TPMJB/K-UI-NeXT/docs/evidence/launch-recovery-disc-stop-2026-10-06.md

# Launch recovery and optical idle

The checksum-batching test `8f7ea7925344` stopped tested games at the detached stage's `INVALID RETAIL MAP`, detail 1. The launch-preparation implementation is restored exactly to working `606f74248d5c` source. Existing GD command fixes, format support and the RAM game catalogue remain. This is a recovery candidate; console confirmation remains required. The precise cause of the failed native handoff is not established.

The boot/recovery menu and SD runtime draw their first screen, then submit firmware `CD_CMD_STOP` before creating the I/O worker. The command uses the existing bounded command adapter: three seconds, then one second for abort recovery. It refuses active DMA and a poisoned adapter. Cleanup ignores held B, and it submits no disc INIT, TOC or read command. Bus/syscall setup is separate from media initialization. The pinned KOS stop command is used directly because its convenience spin-down wrapper has no timeout.

Runtime idle title detection starts parked. Status polling cannot trigger a title read of the existing disc, including through status errors, RETRY, or disc-type changes. An observed lid-open/empty transition permits one identification when media returns. Identification then stops the drive again. Explicit optical applications can start the motor normally; capture and audio ownership are preserved. End-of-operation stop does not interrupt active CD audio. A firmware status syscall cannot guarantee unseen firmware motor behavior, and physical spin-down timing needs console testing.

An SD runtime update adds this behavior with the existing bootstrap disc. The earlier CD boot screen only gains it when that bootstrap itself is updated.

Validation: 56 FAT32/exFAT launch-preparation cases pass under ASan/UBSan: 34 independent exact-CRC/range/fault fixtures and 22 original cooked/background/CE/cancellation/error cases. Every active-operation whole-card SHA256 remains unchanged and successful fixtures pass filesystem-health checks. The restored reader performs 16 IP reads and 33 reads for a 66,537-byte executable. Optical adapter and title-detector tests pass under ASan/UBSan, including held-B cleanup, active-DMA refusal, bounded failed-abort poisoning, type/error flaps and removal/insertion. The 11 workflow-hygiene checks pass. GitHub compiles and checks the native packages before this candidate is delivered; none of these host checks establish physical compatibility or spin-down timing.
