TPMJB/K-UI-NeXT/docs/evidence/sci-async-runtime-reader-2026-10-02.md

# Reusable SCI runtime reader and sustained diagnostic

Recorded 2026-10-02. This implements the next hardware-validation gate after
the [80-read console pass](sci-async-repeat-read-pass-2026-10-02.md). Console
validation of this candidate is pending. Native game reads and CE launch are
unchanged; the [native integration plan](sci-native-async-integration-plan-2026-10-02.md)
records the required cursor, interrupt and memory work.

## Reader contract

The runtime now exposes a serialized `open/begin/poll/finish/cancel/close`
reader. Both the existing quick probe and the sustained test use it. A poll
performs at most eight framing bytes or one DMA-state observation; it never
waits for the in-flight payload to finish. The CPU can return to other work
between calls while receive-only DMA captures the 512 data and two CRC bytes.

Publication still requires completed owned DMA, intact buffer guards, CRC,
an optional expected-sector comparison, and a successful framing handoff.
The diagnostic supplies the expected sector on every read. Without that
optional comparison, the API explicitly reports `baseline_checked=false`.
Generation and handle identity reject stale or copied leases. Each resumed
operation rechecks ownership before touching hardware or receive data.

Cancellation drains an active transfer through bounded polling and discards
its result; closing a pending operation cannot silently abort it. An
incomplete DMA retains its static receive allocation and quarantines the
transport until restart. Unknown SCI module state forbids further SCI MMIO.
The previously console-tested conditional SCI-only reset remains restricted
to a completed, verified payload with trailing overrun.

Review found that ending a slow-only lease could restore BRR without updating
the normal driver's cached speed. A runtime-only helper now reconciles that
cache after verified healthy restoration. It transmits no bytes, changes no
hardware and cannot clear a sticky bus fault. Ordinary verified storage
recovery remains mandatory before report writing.

## The 60-second test

Diagnostics → Storage tests → SCI async probe retains **A: Quick** and adds
**X: 60s stress**. B requests cancellation. The worker pauses existing storage
consumers and unmounts the volume before taking its exclusive lease.

The test obtains each baseline twice through the normal CRC-checked reader.
It selects the first eight sectors and eight more spread through the card's
addressable range, including its last sector. Smaller devices use a bounded
smaller cohort. It then alternates forward and reverse passes over that
cohort at full speed for at least 60 seconds, with a 262,144-read safety cap.
Every read must match its corresponding baseline. The sector tests are
read-only; the final JSON report is the only storage write.

Between bounded polls, the CPU performs independent work and records DMA
count progress. The client allows natural scheduler preemption during bounded
bursts of up to 64 reads and voluntarily yields between bursts. Yielding on
every short DMA poll could otherwise place the receive windows between timer
ticks and weaken the observation. No timer cadence or priority is changed.

An observer temporarily chains the existing KOS TMU0 IRQ handler. It records
real timer interrupts, including those arriving while the reader proves an
owned, incomplete DMA active. It calls the original handler with its original
arguments and does no work after that call. Restoration is verified; a
foreign replacement is preserved and reported. Failure to acquire the hook
does not authorize removing someone else's observer.

The observer uses the pinned KOS handler/scheduler contracts, reviewed in
[timer.c](https://github.com/KallistiOS/KallistiOS/blob/fcfa7d869471591ca1c777543261a7bfea7cb726/kernel/arch/dreamcast/kernel/timer.c),
[irq.c](https://github.com/KallistiOS/KallistiOS/blob/fcfa7d869471591ca1c777543261a7bfea7cb726/kernel/arch/dreamcast/kernel/irq.c),
[thread.c](https://github.com/KallistiOS/KallistiOS/blob/fcfa7d869471591ca1c777543261a7bfea7cb726/kernel/thread/thread.c)
and [thdswitch.s](https://github.com/KallistiOS/KallistiOS/blob/fcfa7d869471591ca1c777543261a7bfea7cb726/kernel/arch/dreamcast/kernel/thdswitch.s).
Voluntary `thd_pass()` does not rearm the primary timer in this revision.
These are interface/semantic references; no DreamShell driver code is used.
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
