TPMJB/K-UI-NeXT/resources/release-v1.7/ftp-busy.png

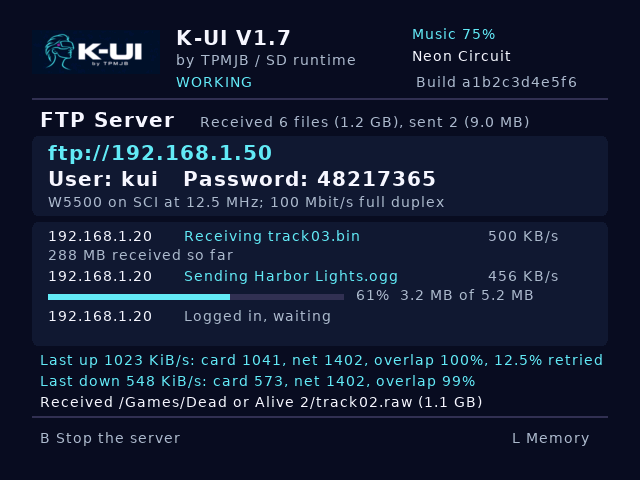
resources/release-v1.7/ftp-busy.png
