TPMJB/K-UI-NeXT/resources/release-v1.7/games-ce-probe.png

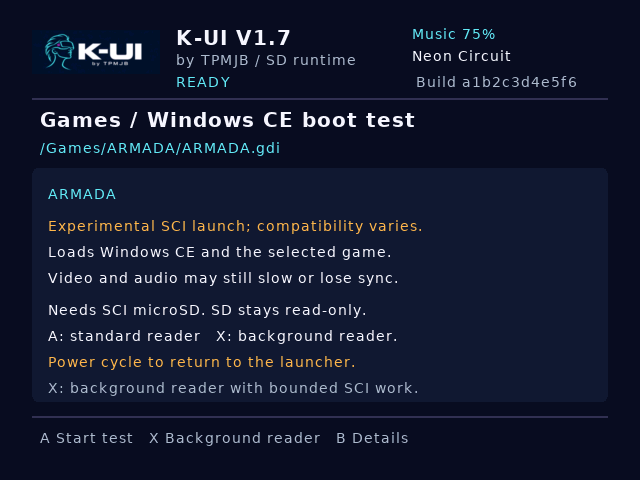
resources/release-v1.7/games-ce-probe.png
