TPMJB/K-UI-NeXT/resources/release-v1.7/home-games.png

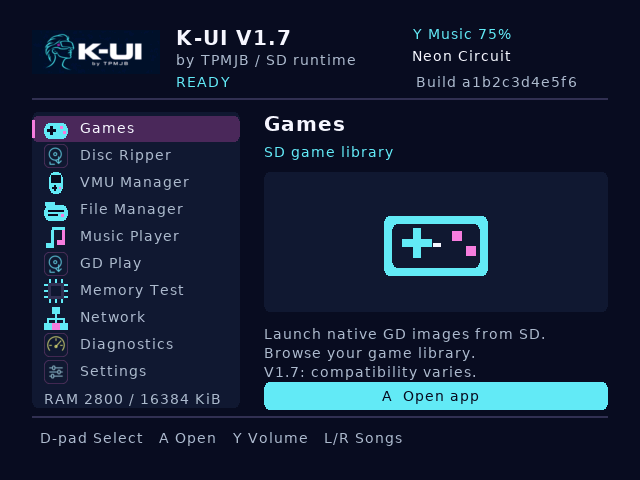
resources/release-v1.7/home-games.png
