TPMJB/K-UI-NeXT/docs/storage-testing.md

# Diagnostics storage tests

Install the updated `/KUI/runtime.kui`, then open **Diagnostics** from the main
menu and press **R** for **Storage tests**. This update works with the existing
boot CD and FAT32/exFAT card. No reformat is needed.

The target is the device selected at boot (SCIF, SCI or IDE/CF). These presets
do not read `bench.cfg` and do not fall back to another device. The original
Diagnostics disc test (A), storage integrity check (X) and save log (Y) remain
available; **Advanced benchmarks** opens the older `bench.cfg` workflow.

## Presets and controls

| Preset | Temporary file per cycle | Request size | Length |
| --- | --- | --- | --- |
| Quick | 4 MiB | 64 KiB | 1, 3 or 5 verified cycles |
| Compare | 16 MiB | 16, 64 and 256 KiB | 1, 3 or 5 samples at each size |
| Soak | 16 MiB | 64 KiB | 5, 15, 30 or 60 minutes |

Quick with one repeat is the default. Soak finishes its current verification
cycle when it reaches the time target, so the actual duration can be longer.
Allow at least the temporary-file size plus 1 MiB free. Filesystem scanning
and saving add time beyond the measured transfer calls.

Use the D-pad to select/change options. An optional **Card nickname** helps
identify results; it is a label you enter, not a detected card model. **Start
test** and **Repeat last test** show the selected recipe for confirmation.
Menu music pauses for the run, then resumes if it was playing. CD audio stops.
The display uses a 2 Hz refresh limit while measuring.

**B** requests a safe stop. Keep the card connected until the worker finishes
cleanup and saves the stopped result. A stopped run is never marked Passed.
Ordinary storage actions are locked while a test runs. Power off before
changing adapters or wiring.

Each run creates a new `/KUI/tests/tNNNNNN/` folder. Its `scratch.bin` contains
a pattern tied to byte position and cycle number. Each cycle writes, flushes,
closes, unmounts, remounts, then rereads and compares every byte. The scratch
file is removed on completion or normal stop. Existing files are never used
as test data. After power loss, an incomplete run is shown as interrupted;
its scratch file may remain in that run's folder.

## Reading and comparing results

The summary shows verified read/write rates, repeated-sample range, worst
read/write call, approximate p95 upper bound, verification outcome and baseline
comparison. Left/Right changes the displayed request size for Compare.
**X Details** shows build, transport, filesystem/cluster size, elapsed time,
verified bytes and error information. A failed save is visible on screen.

**History and baseline** lists the newest eight runs. A opens a result; Y makes
a saved passing result the baseline; X reloads history. All older reports remain
on the card, and a selected baseline remains available even after it leaves
the newest eight. Baseline selection survives reboot. Copy the test folders
with the card if you need their history on a different card.

Comparison requires passing runs with matching recipe, filesystem, cluster
size, music state and display rate. Inactive recipe options are ignored.
Build, transport and nickname may differ and are shown alongside the comparison,
so driver builds and adapters can be compared. Other variables such as card
free space, fragmentation and temperature still matter; the comparison is not
a claim that those conditions were identical.

For an initial session: run Quick once, then Compare with three repeats, select
that result as the baseline, and run a 15-minute Soak. After changing a build or
adapter, repeat the same Compare recipe. Power-cycle between sessions when you
want the same starting conditions.

## What is measured and saved

- Rates time the filesystem read/write calls. Pattern generation and checking
  are excluded; flush time is saved separately. Rates are not raw bus bandwidth
  or end-to-end loading speed. Remounting resets filesystem state but cannot
  guarantee a card's internal cache is cold.
- Quick/Compare report the median of complete verified samples for each request
  size, plus their range. Soak combines all complete verified cycles.
- Every measured call contributes to latency statistics, including calls after
  the first 512. A bounded log2 histogram gives an approximate p95 **upper bound**;
  exact minimum/maximum and counts over 20 ms and 100 ms are also saved.
- Error details distinguish I/O, timeout, CRC and command rejection where the
  transport exposes them. SCI may include the command/response; unsupported
  detail is left absent. Reports retain failure phase, byte offset and FatFs
  status. Cleanup failure is shown separately.

Each completed save contains `result.json`, `result.csv` and a versioned,
CRC-validated `result.bin` used by History. The `STARTED` marker permits detection
of interrupted runs. JSON includes metadata, all samples, latency counters and
errors; CSV has one row per complete sample. Reports omit unfinished samples
from rates while retaining whole-run counters and the failure outcome. Run IDs
do not depend on the console clock.

The first [SCIF soak baseline](evidence/scif-soak-baseline-2026-10-01.md) passed
on 2026-10-01: 21 cycles, 336 MiB written/verified and zero reported errors.
The matching [SCI soak](evidence/sci-soak-baseline-2026-10-01.md) also passed:
15 cycles, 240 MiB written/verified and zero errors. SCI write/read rates were
521.75/528.75 KiB/s versus SCIF's 1,079.94/612.32 KiB/s, respectively 51.69%
and 13.65% lower. This is an accepted initial integrity/performance baseline,
not evidence of a speed improvement.

The [SCI DMA candidate](evidence/sci-dma-design-2026-10-01.md) adds per-run DMA
read/write, polling and failure counts to the Diagnostics log and the existing
message field of passing SCI results. Start with Quick once to check both data
integrity and actual DMA use before another long soak. Raw throughput figures
from different presets are useful preliminary observations, but the saved
baseline comparison still requires matching recipes.

The first DMA build, `cf8e7ea7866b`, then passed the owner's matching 15-minute
Soak: 26 cycles/416 MiB, zero errors or DMA faults, write/read
1,004.62/926.11 KiB/s. Its saved counters establish DMA activation. Preserve
this [DMA result](evidence/sci-dma-soak-2026-10-01.md) alongside the initial
polled SCI and SCIF baselines when assessing further changes.

The cached processing build `a6cb21895c37` passed a subsequent **Quick** run:
4 MiB verified, zero errors/DMA faults, write/read 1,104.35/1,052.72 KiB/s.
Keep this [short result](evidence/sci-dma-cached-quick-2026-10-01.md) separate
from the sustained baseline; its inactive `soak_minutes` setting is not the
actual preset.

New SCI results also include an optional `sci_profile` object in `result.json`.
Its microsecond totals separate DMA setup, transfer, and receive reversal/CRC;
divide by `profiled_rx_blocks` or `profiled_tx_blocks`, not payload bytes or all
DMA attempts. Profiling is enabled only during Storage tests and adds some
timer overhead. Counts cover successful DMA payload operations, including any
metadata within the run; protocol CRC acceptance remains a separate check.
Transfer time includes CPU feeding and completion waits, so it is not a direct
measurement of clock-active time. Commands, card token/busy waits, channel
restoration, polling fallback and filesystem costs are not included in these
phase totals. The Diagnostics log includes the same totals. History and CSV
retain their existing format; the detailed profile is exported only in the
original JSON, while History retains the DMA activity summary.

The first [profiled hardware results](evidence/sci-dma-profile-2026-10-01.md),
build `65fcaafadb98`, passed Quick (run 6, 4 MiB) and five-minute Soak (run 7,
160 MiB), both with zero errors/DMA faults. Quick write/read rates were
1,097.42/1,037.03 KiB/s; Soak reached 1,132.60/1,044.27 KiB/s. The latest
single Quick is slightly slower than a6cb218's Quick, which does not establish
a regression given instrumentation and run variation. The new Soak is faster
than cf8e7ea's fifteen-minute result, but duration and build differences prevent
isolating the latest change. Soak RX means are 331.02 microseconds transfer
and 77.18 microseconds reversal/CRC per sector. These totals identify the
post-transfer check as a candidate for further work; they do not assign all
remaining file-read time to the card or establish a future speed gain.

The subsequent [499bcb53c2d4 Soak](evidence/sci-dma-word-soak-2026-10-01.md),
run 8, passed the same five-minute/160 MiB recipe with zero errors/DMA faults.
Write/read rates were 1,196.64/1,048.89 KiB/s, +5.65%/+0.44% versus run 7.
TX setup fell from 35.96 to 20.21 microseconds per sector, while RX
reversal/CRC increased slightly from 77.18 to 78.18 microseconds. The measured
benefit is write preparation; the small read-rate difference does not establish
a repeatable read gain. Runtime tests do not prove the separate retail
module-wake correction or game DMA/batching behavior. The owner's 29-second
Kasumi-selection-to-first-fight observation is recorded separately; return
counters were not captured, and another capture attempt was deferred.

Build **6cc2abb460b5** subsequently passed Quick run 9 and Soak run 10:
4 MiB and 160 MiB respectively, zero errors/DMA faults. Soak write/read
1,198.32/1,064.87 KiB/s is +0.14%/+1.52% versus run 8; RX checking fell
12.4% to 68.48 microseconds per sector. The matching game counter photo
shows roughly two sectors per step and no enlarged budgets. See the
[reports and separate game-counter interpretation](evidence/sci-grouped-crc-and-game-pacing-2026-10-01.md).
The next experiment changes game pacing, so another Storage soak is not the
next gate: use the same DOA2 load, gameplay/audio and FMV comparison.

Host checks cover real FAT32/exFAT images, corruption and stale-cycle data,
short I/O, cancellation, flush/close/remount errors, scratch ownership and
interrupted result/baseline writes. These tests exercise runtime filesystem I/O;
retail Games readers are separate programs and are not benchmarked here. The
next SCI check is the same DOA2 image using a matching SCI-capable
`/KUI/apps/games/retail-boot.kui`; a runtime-only update does not replace it.
