TPMJB/K-UI-NeXT/docs/experiment-plan.md

# Experiment plan: where the capture time goes, and what to change

This is the historical experiment notebook. Later trips and corrections are
recorded below; consult [the reader handoff](HANDOFF-disc-reader.md) for accepted
hardware results and defaults. The current destination/UI work does not reopen
the acquisition experiments.

The goal is to decide what to build next for capture speed *before* building it.
This document says what is known, what is only a hypothesis, which bench run
settles each open question, and what each outcome means for the work. The
measuring tools are in [benchmarks.md](benchmarks.md); ready-made config files for
every step are in `docs/bench-cfgs/`.

Status of the tooling: the parser, the bench logic (against a fake drive, clock
and scheduler, on real FAT32 and exFAT images) and the UI redraw policy are
tested on the PC, and every console-side file compiles against the pinned KOS
headers. **None of it has run on hardware.** Everything below marked
*hypothesis* or *model* is exactly that until a trip confirms it.

## 1. What the data says today

There are three regimes, and they have different bottlenecks. The percentages
are wall-clock shares from `docs/evidence/` (the builds that used paired reads).

| Regime | Measured | Bottleneck |
|---|---|---|
| **High-density data track** (almost all of a normal game's bytes) | ~373 KiB/s per capture; drive alone ~1450 KiB/s | The CPU: SD write, SHA-256, PIO transfer, in series |
| **Low-density data track** (tracks 1-2, small) | 187 KiB/s paired; disc 63.2%, write 23.3%, SHA 10.7%, CRC32 2.0%, EDC 0.8% | The drive, partly |
| **Audio track** | 57.0 KiB/s paired (MDK2 track 4); disc 88.5%, write 7.2%, SHA 3.6%, CRC32 0.7% | The drive |

Two facts about the audio row matter more than they look:

- **It predates single-read capture.** Commit `f9e8958` (2026-09-17) changed
  capture from paired to single reads; the audio evidence was taken on the
  earlier build. In that run each read of a pair ran at 134.0 KiB/s (read 1) and
  125.3 KiB/s (read 2), so a single read costs about half of a pair and *at HEAD,
  audio should be roughly 2x better than 57 KiB/s* (modelled ~106 KiB/s). As far
  as the repo shows, nobody has measured it since. One capture of one audio
  track answers it.
- **Part of the drive's time looks like per-command overhead.** A 32-sector
  command took 548.6 ms on average against 426.7 ms for 32 sectors at 1x CD speed
  (75 sectors/s): about 122 ms extra per command on average, and the slowest
  command took 2.29 s. Only 4.3% of command time was CPU in the firmware poll
  calls. If the extra time is per command, bigger reads amortise it (Trip 2e). If
  it is per sector (the drive re-reading marginal audio sectors, which the 2.29 s
  outlier hints at), they will not, and the lever is the drive's own retry
  behaviour instead (section 7).

What that means for priorities. For a 1.19 GB disc (Sword of the Berserk's
size), computed from the rates above:

| If the disc were all... | at | takes |
|---|---|---|
| data | 373 KiB/s (today) | 51.7 min |
| data | 680 KiB/s (DreamShell's reported figure) | 28.4 min |
| audio | 57 KiB/s (paired build) | 5.6 h |
| audio | ~106 KiB/s (modelled, single reads) | 3.0 h |
| audio | ~141 KiB/s (drive ceiling) | 2.3 h |

For a music-heavy disc, data-path work barely moves the total: audio dominates. For a
disc that is mostly one big data track, audio is a rounding error and the
data-path work is everything. **Which one your discs are decides what is worth
building.** The TOC lines at the top of any report give each track's type and
size; the split for a disc is one glance.

## 2. Hypotheses, and what would refute each

**H-UI: the UI thread takes 20-35% of the CPU during operations.** Model, not
measurement. `main.c`'s loop runs at the same priority as the worker, redraws
the whole screen in software, and busy-waits for vertical blank inside
`vid_waitvbl` (verified in the pinned KOS: it is `while(!(PVR_GET(...)))`, not a
sleep). Under KOS's 10 ms round-robin, a simulation of that loop takes 22-34% of
the CPU for draw costs of 4-28 ms, and the 28% of optical wait time that the
earlier analysis called "slack" fits. If true, every CPU-bound number measured so
far was taken with a fifth to a third of the machine missing, and *merely
throttling the redraw* would raise them with no restructuring. If false, the
measured numbers are the machine's numbers and only overlap can help.
*Refuted by:* `ui_pct` under ~3% on the hash bench (Trip 1).

**H-overlap: hiding the drive wait behind SD/hash work would help by a large
factor.** True in the model only if the wait is genuinely wait (drive busy, CPU
spinning) rather than PIO work. The model puts a second thread at +20% to +52%
over the best serial loop, depending on the CPU fraction of the optical read
(which nothing has measured) and on whether H-UI holds, and DMA at up to ~+68%.
*Settled by:* the poll-duration histogram (Trip 2a) and how long the drive
tolerates being left unserviced (Trip 2c).

**H-chunk: bigger optical commands are faster.** Today's 32-sector chunk is a
compile-time constant nobody has varied on the optical side. The SD side already
gains ~7% from 128 sectors. *Settled by:* Trip 2a (data) and 2e (audio).

**H-align: SD writes aligned to the 128 KiB exFAT cluster are faster.**
`sd_bytes` writes sizes that are not sector multiples on purpose. If aligned
wins, capture needs a small coalescing buffer that writes exactly 128 KiB at
128 KiB file offsets regardless of chunk boundaries. *Settled by:* Trip 3.

**H-audio: audio's ~122 ms per command is fixed overhead that larger commands
amortise.** *Settled by:* Trip 2e. If it holds, `KUI_CAPTURE_CHUNK` above 32
helps audio by about 20% (four times the sectors per command spreads the same
overhead over four times the data).

## 3. The model

`tools/throughput_model.py` predicts each candidate change from measured inputs.
Stages run in series on one CPU, so `time per KiB = drive + optical CPU + SD +
SHA + CRC32 + EDC`. Two parameters are exposed because the old benches could not
see them and the new ones can:

- `--ui-share` = the `ui_pct` of the hash census at `uihz=full`.
- `--opt-cpu` = share of optical command time spent in poll calls of 100 us or
  longer (the PIO transfer itself; shorter calls are the CPU spinning on a busy
  drive and count as waiting). From a sweep point: the sum of the last three
  numbers of its `BENCH poll ... ms=` line, divided by the command time
  (`bytes / rd`, converted to ms).

For the high-density data regime, with `--opt-cpu 0.35`:

| KiB/s | UI costs nothing | UI takes 28% |
|---|---|---|
| today (chunk 32, UI full, SHA and CRC in the loop) | 373 | 373 |
| UI quiet | 373 | 487 |
| + chunk 128 | 385 | 502 |
| + SHA-256 out of the loop | 494 | 631 |
| + a second thread (ideal) | 634 | 880 |
| + DMA (ideal) | 748 | 1039 |

The overlap rows are upper bounds: perfect scheduling, no switching cost. The
first four rows are serial and need no concurrency. Read across: if H-UI holds,
a quiet UI, chunk 128 and SHA out get to ~631, close to but still under 680,
without a rewrite; if it does not, only overlap (and then only DMA-class overlap)
gets there. For audio (`--optical 134 --opt-cpu 0.05`) the ceiling is the drive:
~106 today, ~114 with a quiet UI, and ~141 is the most anything can reach.

## 4. The trips

Each trip is one config file copied to the card as `KUI/bench.cfg`, then the R
trigger, then wait for READY. The report auto-saves to
`/KUI/probes/pNNNN/diagnostics.txt`. **Run each twice**; one run is not a number.
Paste the `BENCH` lines (or the file) back. B stops safely; lines already printed
stay valid.

### Trip 1: does the UI cost CPU? (`t1-ui-census.cfg`, ~4 min)

One pass of the optical, hash and SD benches per `ui_hz` value: `full`, 8, 2, 0.

Read first, in this order:

1. `BENCH cpu sha256 uihz=full ... ui_pct=` : the cleanest reading, because
   hashing never yields, so the UI gets only its scheduler share.
2. The same `sha256 cyc_b=` across the four passes. It should fall by about
   `ui_pct` from `full` to `0`. **If the census says 28% and `cyc_b` does not
   move, one of the two is wrong** and neither should be trusted.
3. `sd write kib_s` and `optical kib_s` across the passes.

| Outcome | Means | Do next |
|---|---|---|
| `ui_pct` >= 15% and rates rise as the cap drops | H-UI holds | Build the light UI (section 6, item 1), then run Trip 4 |
| 3-15% | Partly; worth the cheap fix only | Light UI, do not expect a jump |
| under 3% | H-UI is dead | Trip 2 decides the rest |
| `optical` ui_pct high but its kib_s flat | The UI only took drive-wait time; free | The UI matters for CPU stages, not the read |

The 8 / 2 / 0 spread is the dose-response: cost per redraw is
`ui ms / (hz x wall seconds)`, which is what the light UI has to fit inside.
Also read `ui_hz=2` as a candidate default: twice a second is a readable progress
line.

**Result (2026-09-19; two runs; exFAT card; a disc whose TOC matches Sword of the
Berserk).** H-UI holds, and by more than the model said. Raw report and parsed
numbers: [evidence/t1-ui-census-2026-09-19.json](evidence/t1-ui-census-2026-09-19.json)
(every derived figure there is computed from the raw log, not typed).

| KiB/s, mean of 2 runs | `full` | `8` | `2` | `0` | 2 vs full | 0 vs full |
|---|---|---|---|---|---|---|
| SD write (chunk 128) | 782.9 | 937.8 | 1122.2 | 1184.5 | +43.3% | +51.3% |
| SD read | 471.7 | 539.5 | 644.3 | 676.5 | +36.6% | +43.4% |
| SHA-256 | 1696.8 | 1960.3 | 2336.4 | 2480.6 | +37.7% | +46.2% |
| CRC32 | 8840.2 | 9893.7 | 12947.7 | 13229.0 | +46.5% | +49.6% |
| Optical @ FAD 45150 | 1194.2 | 1184.0 | 1192.2 | 1196.2 | -0.2% | +0.2% |

- **UI share of the CPU** (census; mean of SHA-256, SD write, SD read): full 31.9%,
  8 Hz 20.7%, 2 Hz 5.3%, 0 Hz 0%. **One redraw costs about 26.5 ms** (26.4 at 8 Hz,
  26.7 at 2 Hz: the two agree, so the cost is per redraw, as modelled).
- **The census and the speed-ups corroborate each other** to within 0.2 percentage
  points, per stage and per pass (the census's `ui_pct` against `1 - rate/rate at 0`).
  Run-to-run spread is 0-0.13% with the UI quiet and 0.7-6.6% at full.
- **The optical read does not care** (drive-bound), so the freed CPU is worth
  nothing to it directly; it matters for every stage that runs on the CPU.
- True CPU cost per byte with the UI quiet: SD write 165 cycles, SD read 289 (which
  includes the CRC16 check), SHA-256 78, CRC32 14.
- **Decision taken: `ui_hz` now defaults to 2.** `ui_hz=full` restores the old loop.
  Idle screens are never capped. What remains is about 5% at 2 Hz, which a lighter
  partial-redraw UI could recover; it is small next to the rest of the plan.
- A `CMD 24 FAILED sense=6/40` at the start of each run is the drive's first INIT
  after a disc change, not an error.

### Trip 1b: is KOS's CRC16 loop worth replacing? (`t1b-crc16.cfg`, ~30 s, no disc)

Times KOS's own `net_crc16ccitt` against three table-driven versions on identical
data in 512-byte blocks (what the SD driver does), and checks they agree. The
driver's CRC16 was **measured directly** by the SD read-CRC on/off run (Trip 3b):
22.2 cycles a byte, 13.4% of an SD write (165.4 cycles a byte) and
7.7% of a read. **Predicted from instruction counts alone, not measured** (KOS's
loop is 28 instructions a byte, the table loop 16, slice2 about 11.5, at the same
~1.3 per cycle): table about 12 cycles a byte, slice2 about 9, nibble slower than
KOS's. A saving of S cycles a byte cuts SD write time by S/165.4 and read time by
S/288.5: for slice2 (S about 13.2) that is roughly +9% on write and
+5% on read. `agree=OK` must appear; on `MISMATCH` ignore the timings. If the
measured saving is under a few percent, leave KOS alone.

**Result, 2026-09-20** (from the default benchmark the T7 session's R press ran; [evidence](evidence/t1b-crc16-and-sd-sizes-from-the-t7-bench-2026-09-20.json)). CPU cycles a byte: KOS 22.7, table 11.7, slice2 8.8, nibble 24.9 (slower than KOS, as predicted); all four agree. On the T7 capture that projects to: slice2 saves about 87 s of 1605 (**+5.7% capture speed**), the table version about 69 s (+4.5%). The SD-write-only figure above is larger because the write is only 64% of a capture. Worth doing after the bigger levers, and at link time (`-Wl,--wrap=net_crc16ccitt`) rather than by patching KOS.

### Trip 2: the drive (`t2a`..`t2e`, ~1 min each)

`sections=sweep` reads sectors with the real PIO command in a bench-only buffer.
Each point prints:

```
BENCH sweep uihz=1 fad=45150 chunk=32 gap=0 svc=0 reads=64 retry=0 rd=.. min=.. max=.. bytes=.. us=.. kib_s=..
BENCH poll fad=45150 c=32 n=a/b/c/d/e      # poll calls by duration:
BENCH poll fad=45150 c=32 ms=a/b/c/d/e     #   <25us /<100us /<400us /<1.6ms /more
```

`rd` is KiB/s inside the read command only; `kib_s` includes the idle `gap`. A
sector-by-sector CRC gate runs per read size on data tracks:
`BENCH verify ... OK` or `MISMATCH`. **A MISMATCH disqualifies that read size
whatever its speed.**

- **2a chunks** (`8..128`): does bigger mean faster? Also gives `opt-cpu` for the
  model from the histogram.
- **2b gap** (0 / 2 / 10 / 40 ms between commands): the drive is idle for well over
  100 ms after every command in today's loop. If `rd` falls as the gap grows, the gap
  itself costs revolutions and back-to-back commands gain more than the model
  says; if it does not, the drive re-arms cheaply.
- **2c service** (0 / 1 / 4 / 10 ms spin after each poll): how long the CPU can be
  away from the drive mid-command. Where `rd` starts to fall is the longest slice
  of SD/hash work a *single-threaded* pipeline may do between polls. **As a rule of
  thumb, at 4 ms or more cooperative interleaving (hash a slice, poll, write a
  slice, poll) is enough and needs no thread; under 1 ms it is too fine and a
  thread or DMA is needed.**
- **2d radius** (four FADs across the big data track): the high-density area is
  constant angular velocity, so rate rises outward. Every earlier optical figure
  is one radius; this is the curve.
- **2e audio** (`8/32/128`, gap 0 / 40 ms): H-audio. Verification is off because
  raw audio can legitimately differ between reads.

**Results, 2026-09-19 (two runs each; exFAT card; the disc whose TOC matches Sword of
the Berserk).** Raw logs and parsed numbers:
[2c](evidence/t2c-service-tolerance-2026-09-19.json),
[2d](evidence/t2d-optical-radius-2026-09-19.json). Every derived figure is computed
from the logs.

- **2c service tolerance (32-sector reads, FAD 45150):** mean `rd` 1239.2 / 1223.7 / 1187.2 / 974.0 KiB/s at 0 / 1 / 4 / 10 ms.
  Loss against the same run's `svc=0`: -2.3% / -7.4% / -24.1% in run 1 and
  -0.1% / -0.7% / -18.5% in run 2. The `svc>0` rates agree between runs
  (0.9% apart at 4 and 10 ms); the `svc=0` rate did not (7.9% apart), which is where
  the difference between the runs comes from. **The drive tolerates about 1 ms of
  CPU-away time between polls with no measurable loss, 4 ms with 0.7-7.4%, and 10 ms
  costs a clear 18-24%.** By the table below that is the cooperative-interleave
  regime with a small penalty: a 4 ms slice is about 4.8 KB of SD write or 10 KB of
  SHA-256. It says nothing yet about whether the SD write can be sliced that finely
  without per-call overhead (Trip 3).
- **2d radius (32-sector reads):** mean `rd` 1251.6 / 1497.8 / 1741.2 / 2003.2 KiB/s at FAD
  45150 / 150000 / 300000 / 450000: **60% faster at the outer edge**, as constant
  angular velocity predicts. Every earlier optical figure here was the slowest point.
  The time in long poll calls (the PIO transfers) is nearly constant across the radius
  (1424 ms at 45150, 1368 ms at 450000, per 4.8 MB), so PIO costs the CPU about the
  same per byte anywhere; what shrinks is the waiting (1051 ms in short polls at
  45150, 381 ms at 450000, or 27.8% of the read down to 16.1%). **What overlap can hide with
  PIO therefore shrinks toward the outer edge**; only DMA (Trip 6) could also hide the
  transfers. Earlier real captures ran near 373 KiB/s (section 1) against 1250-2000
  here, so the drive is not the limit at any radius. All verify lines OK.
- Observation, cause unknown: the second run read slower than the first in the three sweep files of 32-sector reads at FAD 45150 (Trips 2c -7.6%, 2d -5.6%, 6a -5.8%), but not in Trip 1's optical bench at a quiet UI (1196.4 vs 1196.0 KiB/s) and not in a real capture (Trip 5a). Compare runs from the same position in a session and say which one it was in `note=`.

The overlap decision, after Trip 2:

| Finding | Choose |
|---|---|
| service tolerance >= 4 ms and `rd` insensitive to the gap | Cooperative interleave: one thread, deterministic |
| tolerance under 1 ms, or `rd` collapses with the gap | Second thread, or DMA |
| most optical time in the >= 100 us buckets | Little wait to hide; only DMA removes the transfer CPU |

### Trip 3: SD write size and alignment (`t3-sd-sizes.cfg`, ~6 min)

`BENCH sd write ... wbytes=` for 64 KiB to 512 KiB, with and without
preallocation, plus `BENCH lat write` with per-call min / p50 / p95 / max. A size
can win on average and still stall: `slow=` counts calls over twice the median,
`slow_ms` is the time they added, and the largest `max` is the write-behind
buffer a pipeline would have to absorb. Adopt an aligned size only if it wins by
about 5% *and* its p95 is no worse.

### Trip 3b: what does the SD read CRC check cost? (`t3b-sd-crc.cfg`, ~2 min, no disc)

`sd_crc=on,off` with the UI quiet. `check_crc` governs only reads (writes always
compute and send a CRC16 and the card verifies it), so the read-rate difference is
KOS's CRC16 function alone. **Result, 2026-09-19, two runs**
([evidence](evidence/sd-crc-read-cost-2026-09-19.json)): reads 677.0 KiB/s with the check,
733.5 without (+8.3%); writes 1180.7 vs 1180.0, unchanged. That is
**22.2 cycles a byte for the CRC16: 13.4% of an SD write, 7.7% of an SD read**,
matching the compiled loop's instruction count. The check stays on (it is the
read-back's only wire-level protection); the gain is available from a faster
function (Trip 1b).

### Trip 4: the same question on a real capture (`t4-capture-ui.cfg`, 2 x 4 min)

Start a NEW capture, let it run ~3 minutes, press B, save. Change only `ui_hz`
(`full`, then 2) and repeat on the same disc and card. The last census line,
`BENCH cpu operation (setup+capture+verify) ... ui_pct=`, and the CAPTURE phase
average are the answer. This is the check that the bench prediction holds on the
real loop. It will not reach a long audio track in three minutes; for audio on
the real loop, resume a capture that is already inside one (as the MDK2 evidence
run was) and repeat the two settings, and use Trip 2e for the drive alone.

### Trip 5: the capture engine's own choices (`t5a`, `t5b`, `t5c`)

`sections=capture` runs the **real capture engine** on `capture_sectors` sectors of
your disc at every combination of `capture_hash`, `end_readback`, `sample_readback`
and (for the resume timings) `resume_check`, once per `ui_hz`, deleting each job
afterwards. Read `total_kib_s` first: it is the rip plus the end read-back, the
number that decides how long a *finished* dump takes. Then `parts` for where the
capture phase went, `BENCH resume` for the prefix-check cost, and `ui_pct`.

- **5a matrix** (~10 min): hash both/crc32 x end read-back on/off x UI full/2. Settles
  SHA-256's real cost and what the end read-back really adds.
- **5b sampling** (~3 min): `sample_readback` 0/8/32/128, CRC-only. What in-flight
  checking costs at each rate.
- **5c audio** (~3 min): the same engine on an audio track, where the drive should
  dominate and these choices should matter far less. Compare with Trip 2e.

Decision rule: if `crc32` + `end=off` + a small `sample_readback` beats the old default
by the model's margin (about 2.5x in total time on a data-heavy disc), it becomes the
default. If it does not, the model is wrong somewhere and the `parts` lines say where.

**Predictions for 5a, written before the run** (calibrated on Trip 1: 165 cycles a
byte SD write, 289 read, 78 SHA-256, 14 CRC32; chunk 32, inner radius; capture rate
first, total with the end read-back second; KiB/s):

| UI | hash | end read-back | capture | total |
|---|---|---|---|---|
| full | both | on | ~350 | ~176 |
| full | crc32 | on | ~440 | ~222 |
| 2 | both | on | ~430 | ~228 |
| 2 | crc32 | on | ~527 | ~283 |

A miss of more than about 15% on the capture rate means the model is wrong somewhere
and the `parts` lines say where; that is the useful outcome, not a failure.

**Status: the first attempt (2026-09-19, twice) failed before measuring anything**
(`Mount failed: FatFs=3`, `Storage device is not connected`, `BENCH FAILED`; see
[the record](evidence/t5a-capture-matrix-FAILED-2026-09-19.json)). Not a card or
procedure problem: the capture section mounted the card before opening the SD link,
which the console closes after reading `bench.cfg`. A second, quieter bug came out
with it: FatFs keeps the pointer given to `f_mount` even when the mount fails, so the
report save wrote a byte through a dangling stack pointer. Both are fixed and each has
a regression test (section 7). The predictions above stand; rerun 5a on the build that
carries the fix.

**Result, 2026-09-20** (build `bea895bb93b4`; two runs; [evidence](evidence/t5a-capture-matrix-2026-09-20.json)). KiB/s, mean of the two runs, 4096 sectors at FAD 45150. "Finished dump" is the capture plus the end read-back where there is one.

| UI | hash | read-back | capture | finished dump | predicted capture / total |
|---|---|---|---|---|---|
| full | both | on | 399 | 185 | 350 / 176 (+14% / +5%) |
| full | both | off | 400 | 400 |  |
| full | crc32 | on | 515 | 236 | 440 / 222 (+17% / +6%) |
| full | crc32 | off | 514 | 514 |  |
| 2 | both | on | 551 | 258 | 430 / 228 (+28% / +13%) |
| 2 | both | off | 552 | 552 |  |
| 2 | crc32 | on | 717 | 329 | 527 / 283 (+36% / +16%) |
| 2 | crc32 | off | 705 | 705 |  |

- **The fast settings work, and by more than predicted.** Old defaults (full UI, both hashes, read-back on) finish a dump at 185.1 KiB/s; 2 Hz, CRC32 only, no read-back finish it at 704.9: **3.81x**. SHA-256 costs 28-29% of capture speed, the UI cap gives 37-38%, and the end read-back takes 114-119% of the capture time again.
- **The predictions above were too low (+14% to +36% on capture speed).** The model charged the whole media time to the capture. The parts lines show otherwise: disc time is 28.3 ms per 32-sector chunk at 2 Hz/CRC32, only ~15% above the 24.7 ms of the fastest command in the Trip 6a sweep, which is a command whose data the drive had already buffered. The drive reads ahead while the CPU writes to the SD card, so most of that overlap is already happening. The UI effect was also larger than modelled (37-38% against the ~23% predicted).
- **Where a chunk goes** (2 Hz, CRC32, no read-back, 104.3 ms): SD write 67.0 ms (64%), disc 28.3 ms, CRC32 5.8 ms, EDC 2.9 ms. The SD write is the hard floor: the card is driven by bit-banging the serial port's pins at about 143 cycles a byte plus 22 for KOS's CRC16 (Trips 1 and 3b), a peripheral-bus limit that the drive, the hashes and the UI cannot change.
- **What is left, as arithmetic from those parts (a projection, not a measurement):** DMA that overlaps the 28.3 ms transfer with the SD write (Trip 6a, experimental build), a table CRC16 (KOS's loop is ~13% of the write, ~9 ms; Trip 1b), and 1 Hz instead of 2 Hz (~2.6 ms) could together approach ~67 ms a chunk, roughly 1100 KiB/s: about 1.5x from here, and not more.
- The full-disc estimate for Trip 7 follows: track 3 is 1,185,760,800 bytes, which at 704.9 KiB/s is about 27 minutes (the outer radius is no slower). The old defaults would have taken about 104 minutes at their inner-radius rate.
- The resume prefix check with `check=full` re-reads the whole prefix (606.8 KiB/s here); `check=size` takes 4 ms but cannot see a corrupted prefix.

**Trip 6a on the default build (2026-09-20; [evidence](evidence/t6a-pio-only-2026-09-20.json)).** DMA and the competing thread were skipped, as designed: they are in the experimental build only. The PIO points show 32 sectors beating 128 by 6% at FAD 45150 (1245 vs 1168 KiB/s), so the capture engine's command size is right. **Trip 1b was rejected** at `bench.cfg line 1: expected key=value` in both runs, so nothing was measured ([record](evidence/t1b-crc16-rejected-2026-09-20.json)); the loader now skips a UTF-8 byte-order mark and says what a bad line starts with.

**Result, 2026-09-20** (two runs; [5b](evidence/t5b-capture-sampling-2026-09-20.json), [5c](evidence/t5c-capture-audio-path-2026-09-20.json)).

**5b, sampled read-back.** Re-reading one 32-sector chunk costs **166.0 ms**, the same at every
setting, against 102.4 ms to capture one. Measured time cost: 22.2% at
`sample_readback=8`, 5.6% at 32, 1.3% at 128; the model
(cost per sample / (chunk time x N)) reproduces those and gives 2.5% at 64 and 0.6% at 256. On a
26.7-minute capture that is 0.3 minutes at N=128 and 0.7 at N=64. What it buys is small:
at N=128 it re-reads 0.8% of the chunks, which catches a card that is failing systematically but
verifies nothing. `resume_check=size` finished in 3.8 ms, and still cannot see a corrupted prefix.

**5c, the audio code path.** At crc32 with no read-back it is +2.5% faster than the data path
(722.5 against 704.9 KiB/s), matching the 2.8% EDC share of Trip 5a; every parts line shows
`edc=0`. With SHA-256 on, the difference vanishes (-0.0%, -0.4%). **But FAD 63000 is a DATA
track on this disc**, so this measured the audio path on data sectors and says nothing about how fast a
real audio track reads; an audio-heavy disc (MDK2, 29 audio tracks) is still untested. The bench now
warns when `capture_fad` is not inside a track of the configured `capture_type`.

### Trip 6: GD-ROM DMA, and what a second thread would see (`t6a-dma-probe.cfg`, ~2 min)

**Experimental, and not in the default build**: it needs `make diagnostic KUI_EXPERIMENTAL=1` (see
section 7, 2026-09-20). Without it the run prints `BENCH dma skipped` / `BENCH spin skipped` and only
measures PIO. The only route to overlapping the drive with SD and hash work that
does not depend on a plain thread getting the CPU promptly is to stop spending CPU on
the transfer. This trip finds out three things at once, on the real drive:

1. **Does DMA of raw 2352-byte sectors work, and are the bytes identical to PIO?**
   `BENCH dma check ... result=` and a CRC gate per read size (`BENCH verify ... mode=dma`).
2. **How fast is it against PIO at the same size, and how much CPU does it leave?**
   `rd=` on `mode=dma` points against plain ones; `free=` is the share of the CPU a
   competing thread got (100% = it lost nothing).
3. **What would a plain thread cost the drive today?** The PIO points with `free=`,
   against the same PIO points without: an SD-writing thread at equal priority is
   exactly a competitor that never sleeps.

| Finding | Means | Choose |
|---|---|---|
| DMA `rd` >= PIO, `free` >= 90% | DMA hands the CPU back at no cost to the drive | An SD/hash worker thread beside a DMA reader: the overlap design with the highest ceiling |
| DMA `rd` below PIO by more than 10%, `free` ~99% | A real trade | Compute the overlap ceiling from both rates before committing |
| PIO `free` 40-60% and `rd` within 5% of PIO alone | A plain thread already works | Thread split with PIO: simpler, no DMA risk |
| PIO `rd` falls sharply with a competitor | PIO needs the CPU promptly | DMA is the only way to overlap |
| `dma check ... FAILED` | DMA never completed by polling | Reboot. Next step is an interrupt-driven variant (install KOS's `asic_evt` handler, wait on a semaphore) |
| `dma check ... MISMATCH` | DMA returns different bytes: a cache, alignment or protocol problem | Do not use DMA; `reported_bytes` in that line is the first clue |

**Result, 2026-09-20** (experimental build `f54c8cc44068`; two runs; [evidence](evidence/t6a-dma-probe-2026-09-20.json)).
**It works, and it is the outcome the decision table called the best case.**

| chunk | mode | competing thread | rd KiB/s | worker CPU | CPU used |
|---|---|---|---|---|---|
| 32 | PIO | no | 1232.2 | 3756 ms | 98.0% |
| 32 | DMA | no | 1185.5 | 34 ms | 0.9% |
| 128 | PIO | no | 1156.6 | 3971 ms | 97.6% |
| 128 | DMA | no | 1158.4 | 18 ms | 0.4% |
| 128 | PIO | yes | 1032.0 | 1538 ms | 33.3% |
| 128 | DMA | yes | 1154.4 | 19 ms | 0.5% |

- **The bytes are identical.** Both runs' `dma check` passed with the same CRC32 as PIO, and all 8
  `BENCH verify` lines matched the PIO reference at both read sizes.
- **DMA costs the CPU nothing** (0.4-0.9% against PIO's 97.6-98.0%) and is **not slower** at the size a
  capture uses (1158.4 against 1156.6 KiB/s at chunk 128), even though the probe polls with sleeps and so
  carries up to a 10 ms tick of completion latency.
- **A competing thread costs a PIO read 10.8-12.7% but costs a DMA read nothing.** That settles row 4
  of the table in section 6: a plain thread split with PIO pays for itself, DMA does not.
- **Projected: 26.7 minutes becomes about 19.4 (27.6% faster), or about 17.3 with the CRC16 and CRC32
  replacements too.** That is `max(CPU work, disc)` instead of their sum, an ideal bound: real
  double-buffering cannot overlap the first read or the last write and is not free to switch.
- Cost of the probe itself: +308 KB of BSS for its static buffer. A production double buffer needs
  two chunk buffers (147 KB at chunk 32), not that.
- The `free=` percentages are soft (the spin calibration differed between runs, 724 against 995
  iterations/ms, and run 2's UI census differs); the worker-CPU milliseconds are the solid number
  and the two runs agree on them.

### Trip 9: does the overlap actually work? (`t9-pipeline.cfg`, ~3 min, experimental build)

A capture's inner loop - read a chunk, write it to the card, CRC32 it - three ways on the real
drive and card, writing no dump. **Result, 2026-09-20, two runs**
([evidence](evidence/t9-pipeline-overlap-2026-09-20.json)):

| row | KiB/s | read ms | write ms | crc ms | worker idle ms |
|---|---|---|---|---|---|
| pio-sequential (today's engine) | 752.9 | 3435 | 8308 | 750 | 148 |
| dma-sequential | 846.3 | 2020 | 8380 | 714 | 2024 |
| dma-overlapped | **1009.8** | 153 | 8397 | 742 | 260 |

- **92.4% of the read time disappears behind the SD write**, and the overlapped row lands
  only **1.9% above the floor** of write plus CRC32 alone. There is almost nothing left on the
  read side to recover.
- **34.1% faster than what the engine does today**, 19.3% over sequential DMA.
- **The bytes are identical**: one CRC32 (`66f88083`) across all six rows.
- The census says where it comes from: sequential DMA leaves the worker idle 2024 ms while
  the drive works; overlapped leaves 260 ms, having spent the rest writing.
- Sequential DMA alone is already 12.4% faster than PIO: a DMA read of buffered data costs
  less wall time than pulling the same bytes through the CPU.
- **Projected onto the real T7 capture: 26.7 minutes becomes about 19.8**, or about
  17.7 with the CRC16 and CRC32 replacements too.
- What this is NOT: the pipeline has no EDC check, no checkpoints, no SHA-256, no retries and no
  resume. It measures the loop, not the engine.

**Built, 2026-09-20: the overlapped capture engine (`capture_read=dma`, Trip 10).** `kui_capture`
now double-buffers: the DMA read of chunk N+1 is begun as soon as chunk N is in hand, and runs
while N is written and hashed. It is opt-in and defaults to PIO, and the console only offers the
DMA ops in the experimental build. Any chunk it cannot overlap falls back to the ordinary PIO
read, which keeps the retry and recovery behaviour unchanged. Two bugs the host suite caught
while building it: a fatal DMA result was falling back to a PIO retry instead of stopping, and
`sample_readback` compared against `job.data` when the chunk could now be in the second buffer
(the existing sampled read-back scenario failed, which is what it is for). What is NOT yet
measured: the engine's real rate on hardware (Trip 10) and a full disc verified on a PC.

**Result: it works, and it is correct.** Trip 10 ([evidence](evidence/t10-capture-dma-2026-09-20.json)) measured the
real engine at **+34.8%** (715.6 to 964.9 KiB/s on MDK2), matching Trip 9's +34.1% for the bare loop.
Trip 11 ([evidence](evidence/t11-real-capture-dma-2026-09-20.json)) then ripped all of Sword of the Berserk
with it: **19.6 minutes against 26.7 with PIO, 985.9 KiB/s, +36.3%**. Disc time fell from 438.8 s to
5.9 s (98.7% hidden) while every other part stayed within a second. The console's TOSEC check
matched every track, which proves the DMA read byte-perfect, and the PC check matched the reference
on all three tracks, which proves the card wrote it correctly. The result is byte-identical by
SHA-256 to both earlier captures of the disc. **The SD write is now 87% of a capture.**

**Trip 12, MDK2 (31 tracks, 27 audio), 2026-09-20** ([evidence](evidence/t12-mdk2-capture-dma-2026-09-20.json)):
19.6 minutes, 1011.7 KiB/s, TOSEC match on all 31 tracks on the console and again on the PC. The
first hardware test of DMA on audio tracks, and of the PIO fallback at 31 track boundaries.
**On that evidence DMA is now the default (`capture_read=dma`) and is in every build**; only the
blocking probe and its competing thread remain experimental.

Caveats that shape how to read it: the DMA probe **polls** rather than taking the
interrupt (this runtime never starts KOS's CD-ROM subsystem, so nothing installs
the handler), so completion is noticed up to one 10 ms tick late, about 8% at chunk
32 and 2% at chunk 128; compare at chunk 128. It uses a fixed buffer with guard
bytes, does its own cache maintenance (a one-register `ocbp`/`ocbi` loop: KOS's helper
did not compile on the CI toolchain), and turns itself off for the rest of the boot after
any failure. Nothing here
writes to the card or the disc.

### Trip 7: one real, complete capture with the fast settings (`t7-real-capture-fast.cfg`)

The bench times 4096-sector slices of the engine. This is the only test that proves a
whole disc, ripped with the fast settings (`ui_hz=2`, `capture_hash=crc32`,
`end_readback=off`), comes out **byte-identical** to a known-good dump, and it is the
first time the CRC-only, no-read-back path runs on hardware as a real capture. Use the
Sword of the Berserk disc, whose correct CRC32s are known
([reference](evidence/sword-of-the-berserk-reference.json)). Steps: copy the config to
the card as `KUI/bench.cfg`; on the Capture page press **A** (a NEW dump, not X: a
resumed job keeps the hash mode it started with); let it finish. It reports
`CAPTURED`, not `SAVED DATA VERIFIED`, because the read-back is off; the proof is on the
PC: `python3 tools/verify_dump.py <new folder> --reference
docs/evidence/sword-of-the-berserk-reference.json`. Pass means three `PASS` lines with
CRC32 `bcec7767`, `0ff934e3`, `2cfb5dcb` and no reference mismatch. If the two
catalogue files are in `KUI/`, the console report also names the match. 5a has now said which settings are fastest (its result above); at its rate track 3 should take roughly 27 minutes, and it changes only how the dump is *checked*: the disc is read exactly as before.

**Result, 2026-09-20** (build `bea895bb93b4`; [evidence](evidence/t7-real-capture-2026-09-20.json)). The whole disc took **26.7 minutes** (1605 s, average 723.5 KiB/s; track 3 alone 724.6 KiB/s) with 0 retries in 15,797 reads. Trip 5a's inner-edge rate predicted 27.4 minutes for track 3 and it took 26.6 (-2.7%), and the time split (SD write 63.8%, disc 27.3%, CRC32 5.6%, EDC 2.8%) matched the bench's. Against the old defaults that is roughly 3.9x (an estimate: about 105 minutes at Trip 5a's old-default rate; no old-default run of this disc was timed).

Verification came in two independent parts:
- **On the console:** `Reference check (TOSEC): FULL TRACK MATCH`. That compares the CRC32 accumulated *while reading*, so it proves the disc was read correctly; the log also says `saved data NOT re-read`.
- **On the PC:** `SAVED DATA VERIFIED` (every saved file matches the CRC32 the console recorded), and the reference comparison passes on all three tracks (CRC32 and size everywhere; SHA-256 for tracks 1-2). All three tracks are byte-identical by SHA-256, CRC32 and size to the capture made on 2026-09-17 with SHA-256 and a full read-back, which also corroborates that capture's track 3 SHA-256.

A trap: `verify_dump.py --reference docs/evidence/...` takes the path relative to the directory you run it in. Run it from the repository root, or write `../docs/evidence/...` from `tools/`; the error now says where it looked.

## 5. Reading the new lines

- `BENCH pass n/m uihz=...`: the UI setting every line until the next pass line
  belongs to. Every result line also carries `uihz=`.
- `BENCH cpu <what> ... wall= wk= ui= oth= ui_pct=` (ms): the scheduler's
  per-thread CPU accounting over that measurement. `wk` includes busy-polling, so
  a high `wk` in an optical measurement is not necessarily work. It has 1 ms
  granularity that averages out over many switches: ignore intervals under ~1 s.
  `oth` is the idle, reaper and kernel threads.
- `BENCH capture|resume ...` (Trip 5): see [benchmarks.md](benchmarks.md#the-experiment-layer).
  `capture` is the capture phase alone; `total` adds the end read-back; `parts` is the
  split by stage in ms.
- `BENCH lat write|read ... n= min= p50= p95= max= slow= slow_ms=` (us): every
  `f_write`/`f_read` in the run, up to 512 calls.
- `BENCH hash ... crc16-kos|table|slice2|nibble cyc_b=` and `BENCH hash ... crc16
  agree=OK|MISMATCH` (Trip 1b): the SD driver's CRC16 against faster versions.
- `BENCH dma check ... result=`, `BENCH sweep ... mode=dma`, `... free=` and `BENCH spin
  calibration` (Trip 6): `free` is the CPU share a competing thread got, in percent,
  against its own count with the worker asleep.
- Lines wrap at 76 characters in the on-screen log, so a long line can appear as
  two; join them before parsing.
- The log holds 768 lines. A large sweep can overflow it (the report says
  `Log truncated`); split it across runs.
- Compare only runs with the same disc, card and drive temperature, and put those
  in `note=`.

## 6. Candidate changes, in the order the evidence would justify them

Gains are for the high-density data regime and come from the model, so they hold
only if the hypothesis they depend on does.

| # | Change | Model gain | Depends on | Risk |
|---|---|---|---|---|
| 1 | **UI redraw cap, now the default (2 Hz)** | +43-51% on SD write, measured | Done (Trip 1) | None; `ui_hz=full` restores the old loop. A lighter partial-redraw UI could recover the remaining ~5% |
| 2 | Capture chunk 128 (SD write +7%, optical unknown) | +3% | Trip 2a | Low; buffers grow to 301 KB and 602 KB |
| 3 | SHA-256 out of the capture loop | +28-29% **measured** (Trip 5a) | Done as an option (`capture_hash=crc32`); the default is still `both`; Trip 7 decides | Medium; a format change |
| 4 | Overlap the drive with SD/hash work, via GD-ROM DMA | **27.6% measured-and-projected**: 26.7 min -> 19.4 (17.3 with items 5-6). DMA proven on hardware: same bytes, 0.4% CPU, no cost to the drive | Trip 6a: done | High: double-buffering the capture loop, with checkpoint/cancel/retry correctness at every interleaving |
| 5 | Aligned, coalesced SD writes | 0-8% | Trip 3 | Low |
| 6 | Table-driven CRC16 in KOS's `sd.c` | **+5.7% on the capture** (slice2; projected from the measured microbenchmark, Trip 1b) | Trip 1b: done | Low to medium: a link-time `--wrap`, no KOS patch |
| 7 | Faster SHA-256 in C | +3% | none | Low; compiles to ~69 instructions per round today |
| 8 | Audio: larger commands | ~+20%? | Trip 2e | Low |

**Item 3 is decided: SHA-256 comes out of the per-byte path.** The maintainer's
call, after checking what it is for: CRC32 verifies well enough for these rips,
and the earlier GD Ripper (K-UI_DS) never had SHA-256 at all. Its verification is
the design to copy 1:1 (section 6a). SHA-256 stays only in the one-time disc
identity hash (about 0.1 s). Removing it is a format change (checkpoint,
manifest schema, profile version), so it is a patch of its own.

## 6a. Verification: how the old GD Ripper checked in seconds

The old ripper's end-of-rip verification took seconds because **it never re-read
the files.** Its report says so in words: `hash_origin: disc stream / saved
checkpoint (no storage read-back)`. It took the CRC32 accumulated during the rip
(kept in a CRC journal, `gd_crc_checkpoint`, so a resume did not re-read either)
and looked up `(track, size, CRC32)` in a bundled Redump and TOSEC catalogue
(1,245 games, 9,545 tracks; one streaming pass over two small files). A slower
"storage read-back" mode existed separately.

That is the "stream verification" of this project's discussions: the running
CRC32 *is* the verification, and the catalogue is the independent reference that
makes it mean something. It also shows why the console's end pass is the wrong
place for the exhaustive check. A re-read proves only that the card holds what
the drive returned; a catalogue match proves the bytes equal the canonical dump.

**It works on K-UI-NeXT's dumps today.** The complete Sword of the Berserk
capture in `docs/evidence/` matches TOSEC on all three tracks, sizes and CRC32s
identical (track 1 `bcec7767`, track 2 `0ff934e3`, track 3 `2cfb5dcb`), and the
Redump catalogue's USA entry for track 3 carries the same CRC32. So the capture
format, including the track boundaries the `typegap150` profile chooses, is
canonical for that disc, and the check the report has always said was missing
("No independent reference compared") costs a second. The MDK2 evidence run
cannot match yet: the Redump catalogue lists only MDK2's track 31, which that
stopped job never reached.

The end pass matters more than it looks. On the Sword disc the model puts it at
about half the whole job in every scenario (55 min after a 52 min rip today; 44
after 41 with SHA out), because it is bound by SD *read* speed (~458 KiB/s),
which is slower than SD write. Dropping SHA trims it by a fifth; only not doing
it on the console removes it. With SHA out and a catalogue check in place of the
end pass, the whole job is about 41 min instead of about 107 (model).

What is built and what is next:

| Step | State |
|---|---|
| Catalogue lookup at the end of every capture and verify (`src/core/known_dumps.c`, `data/known-dumps/`, packaged to `KUI/`) | **Built, host and image tested.** Additive: nothing removed |
| Drop per-track SHA-256: `capture_hash=crc32` (checkpoint flag, schema 2 manifest, `verify_dump.py` accepts both) | **Built as an option**; default unchanged |
| Skip the automatic end pass: `end_readback=off` (CRC-only jobs; Verify stays as the read-back mode) | **Built as an option**; default unchanged |
| Resume without re-reading the prefix: `resume_check=size` (CRC32 continues from the checkpoint; today 212 s per 72 MiB, about 50 min for a resume at 90% of Sword) | **Built as an option**; default unchanged. It cannot see a corrupted prefix (tested and documented) |
| In-flight sampled read-back: `sample_readback=N` | **Built as an option** |
| Measure all of it on the real engine: `sections=capture` (Trip 5) | **Built** |
| PC-side exhaustive check | Exists: `verify_dump.py` recomputes CRC32 from the files |

The approach, agreed: build every candidate as a runtime option that defaults to
today's behaviour, measure them all on the real engine in one boot (Trip 5), and
choose defaults from the numbers. Not yet built as options, and why: a runtime
capture chunk size and coalesced/aligned SD writes each restructure a buffer path
(the guarded disc read buffers; the write path with its checkpoint ordering), and
Trips 2a and 3 already measure their two halves in isolation. Their results say
whether either is worth that restructuring. The overlap architectures (cooperative
interleave, a second thread, GD-ROM DMA) are larger still, and Trip 2c decides which
of them is even viable.

Two limits to keep in mind. A whole-track CRC cannot locate a bad sector; that is
why the old ripper also checked each data sector's sync, address, EDC and ECC,
and re-read only flagged sectors. And on audio, single reads mean nothing checks
the read itself, so a catalogue match (or a second dump) is the check there.

## 7. Dead ends and corrections, so they are not retried

- **SCI/DMA SD transport.** Failed to initialise on hardware (errno 11): the
  adapter is SCIF-wired, so DMA for the *SD card* is ruled out. That leaves the
  SD side CPU-bound, so overlap can only come from hiding the drive behind it
  (a thread, cooperative interleaving, or DMA on the *GD-ROM* read; a probe for that
  last one is built, Trip 6, and is still untested on hardware).
- **Sending CRC 0xFFFF on writes.** An earlier analysis proposed it
  (~939 KiB/s). **It is wrong.** KOS's `kernel/arch/dreamcast/hardware/sd.c`
  (line 433) sends CMD59 with argument 1 at init, so the card *verifies* every block's CRC16, and
  `write_data()` always computes and sends one. `check_crc` governs only the read
  side. Sending 0xFFFF would fail every write block. Skipping the check would also
  need CMD59 with argument 0, which removes the card's own wire-level protection
  of every write. A faster CRC16 (item 6) recovers most of the time and keeps it.
- **The CRC16 cost of 30.7 cycles a byte** quoted earlier was wall time with the UI
  running. Trip 1 corrects it: about 21 cycles a byte of CPU, roughly 13% of an SD
  write. The gain from replacing it is correspondingly smaller (Trip 1b).
- **The capture bench that could not run (2026-09-19).** The bench's capture section
  mounted the card before opening the SD link, and its cleanup after every run mounted
  it after the console adapter had closed it; the first would not mount (T5a failed
  in seconds) and the second would have left every bench job on the card. Fixed by
  making the bench own the link for the whole section. **Why the tests missed it:** the
  host harness attached the card once and offered no `reconnect`, so nothing could
  observe the link closing. It now models the console (closed at the start, opened only
  by `reconnect`, closed at the end); the capture scenario fails without the fix. The
  lesson for the next section that touches the card: run it on the console before
  trusting a host pass.
- **A failed mount left FatFs pointing at freed memory.** `f_mount` registers the
  caller's `FATFS` before it tries, and keeps it after a failure; every caller then
  returns and drops the object. `kui_mount`, the only registration site, now unregisters
  on failure. The `mount-fail` scenario trips AddressSanitizer without it.
- **The console is not `__SH4__` (2026-09-20; two failed CI builds).** The DMA probe called KOS's
  `arch_dcache_purge_range` and the CI compiler (GCC 15.2, `sh-elf`, `-m4-single`) rejected it: `cannot find a
  register in class GENERAL_REGS while reloading asm`, at `arch/cache.h:126`. That helper is one inline asm with
  eight memory operands plus a register, and the allocator could not satisfy it once inlined into the probe. It
  compiles on every compiler available on a PC (Ubuntu's `sh4-linux-gnu` GCC 13.3, 14.2 and 15.2.0), so it can
  only be avoided, never detected here. My first fix (one-register `ocbp`/`ocbi` loops, chosen with
  `#ifdef __SH4__`) **did nothing on the real build**: GCC defines a different macro for each SH-4 mode,
  `__SH4__` only for plain `-m4`, and KOS builds with `-m4-single`, which defines `__SH4_SINGLE__`. So the test was
  false there, the host-test branch was compiled, and KOS's helper came straight back. The CI log showed it in its
  first line (`from src/dreamcast/disc.c:4`, a host-only include). The same wrong test would also have left the
  DMA buffer's address unmasked: a hardware bug in code that had never run. Now there is one `KUI_ON_CONSOLE` in
  `platform.h` (true for every SH-4 macro and for KOS's `_arch_dreamcast`), raw toolchain macros
  are forbidden anywhere else, and `tests/test_asm_audit.py` runs the preprocessor over `disc.c` under each macro
  set and requires the console branch for every one; with the bug put back, it fails. The PC compile checks now
  also run with the CI's macro set (`-U__SH4__ -D__SH4_SINGLE__`). **Lesson: the CI log is the source of truth
  about the toolchain; an assumption about it is not.** In that failed run every file after `disc.c` compiled
  clean (`crc16.c`, `options.c`, both `bench.c`), so this was the only defect.
- **Experimental code is opt-in, and the CI reports its errors at the end of the log.** The DMA probe and the
  competing thread compile only with `make diagnostic KUI_EXPERIMENTAL=1`, so they cannot break the build the
  capture engine ships in. The CI runs `make -k` and, after a failure, prints `BUILD FAILED: THE ERRORS, IN ONE
  PLACE`.
- **The CI log that broke packaging (2026-09-20).** The error digest added to the compile step wrote its log
  to `build.log` in the checkout. `record_build.py` (at link time) and `package.py` both refuse a dirty tree, and an
  untracked file counts, so a build that compiled and linked still died at packaging with "Commit source changes
  before packaging". The log now lives in `$RUNNER_TEMP`, and `tests/test_workflow_hygiene.py` runs the real step
  text in a scratch git repository (build succeeding and failing) and requires a clean tree afterwards; with the
  bug put back it reports `?? build.log`. **Lesson: a CI change is code with downstream consumers; read what runs
  after it.**
- **`verify_dump.py --reference` and the working directory (2026-09-20).** After a clean `SAVED DATA VERIFIED` the
  reference step failed with "Missing/unsafe metadata: sword-of-the-berserk-reference.json", because the relative
  path was taken from `tools/` (it looked for `tools/docs/evidence/...`). Not a data problem: reproduced exactly, and
  the real loader and comparison pass on the hashes that were reported. The message now names the absolute path it
  looked for and says relative paths are taken from the current directory; a symbolic link is called a link.
- **Two runs that measured the wrong thing, and said nothing (2026-09-20).** A Trip 5b run went out with the
  K-UI boot CD still in the drive: a CD with no high-density area, so the capture section printed one skip line
  and the run ended `BENCH complete`, which reads like success. The same evening, Trip 5c ran with
  `capture_type=audio` at `capture_fad=63000`, which on that disc is inside a DATA track, so it measured the
  audio code path on data sectors (useful, but not the question asked) with nothing in the log to say so. Two
  fixes: `kui_bench_fad_note` (a pure function in the core, unit tested) warns before a long run when
  `capture_fad` is not inside a track of the configured type or is off the disc entirely, and a bench that
  measured nothing now ends `BENCH complete but NOTHING was measured` instead of `BENCH complete`.
  **Lesson: a measurement that silently answers a different question is worse than one that fails.**
- **The example config could never be used (2026-09-20).** `/KUI/bench.cfg is larger than 2048 bytes; ignored`
  stopped a Trip 5c run on MDK2 before it started. The only shipped file over that limit was
  `docs/bench.cfg.example` (5347 bytes) — the file whose name invites copying it to the card. The limit is now
  8192 bytes (6 KB of BSS out of ~14 MB free), the message names the fix, and `tests/test_options.c` fails if any
  shipped file exceeds the runtime's limit. The run did show the engine at 545.4 KiB/s on MDK2's data track 1
  with the old defaults, within 1.0% of Trip 5a on Sword, and a clean stop-and-checkpoint on a 31-track
  disc. **Lesson: a limit that the project's own example violates is a bug in the limit or the example.**
- **"Audio is drive-bound" was wrong (2026-09-20).** The plan and `t5c-capture-audio.cfg` assumed audio tracks
  would be limited by the drive, so the CPU choices would matter less there. A full MDK2 capture says otherwise:
  audio runs at 539.8 KiB/s against 553.0 for data, 2.4% SLOWER, with the same mix (SD write 47.0%, SHA-256 22.9%).
  Audio skips EDC (2.2% of a data track) but its raw transfer costs more per byte (2119.7 against 2534.6 KiB/s),
  which cancels it. So every result measured on Sword carries over to an audio-heavy disc, and no separate audio
  tuning is needed. [Evidence](evidence/mdk2-full-capture-resume-verify-2026-09-20.json).
- **The 28% "slack".** The earlier analysis called the worker's yielded time idle
  slack a second thread could reclaim. It was the UI thread running. That is the
  reason Trip 1 exists.
- **Drive speed.** The pinned KOS has no speed API. The BIOS has `CD_CMD_SET_MODE`
  (31) with four words `[speed, standby, read_flags, read_retry]` and
  `CD_CMD_REQ_MODE` (30), which writes those four words to a caller buffer
  (layout from Flycast's BIOS emulation, `core/reios/gdrom_hle.cpp`); the same
  code base notes speed "doesn't seem to be settable, or perhaps not for
  GD-Roms". Not attempted. If audio turns out to be the priority and Trip 2e shows
  the drive is not the limit, a read-only `REQ_MODE` query is the safe first step.
  `read_retry` is the more plausible lever (it may explain the 2.29 s outlier
  commands), but lowering it trades data quality for speed and needs a decision.

## 8. Questions only you can answer

1. **What share of your discs' bytes is audio?** This decides whether the data
   path or the audio path is where the hours go.
2. **Which regime was DreamShell's 680 KiB/s measured in, and what does it get
   on audio?** If it rips audio well above ~140 KiB/s, the drive has headroom
   this project has not found.
3. ~~Is SHA-256 in the verify pass acceptable?~~ Answered: SHA-256 is not
   needed; CRC32 is enough (section 6a).
4. **How much on-screen progress do you need during a capture?** That sets the UI
   rate the light UI has to fit inside.

## 9. Assumptions worth checking

- The UI scheduling simulation models KOS's round-robin and the loop in
  `main.c`; it shows the hypothesis is consistent with the code, not that it is
  true.
- `ui_hz=0` freezes the screen while an operation runs. B still works (the
  controller is polled every loop), but this is by code reading and the PC-side
  policy test, not a hardware check.
- The census reads KOS's per-thread CPU time (`thd_get_cpu_time`). It has 1 ms
  granularity and includes the running thread's current slice; both are handled,
  but neither has been observed on hardware.
- The catalogue check has never run on the console. It is tested on the PC
  against the real bundled catalogues and on FAT32/exFAT images, and every
  touched console file compiles against the pinned KOS headers.
- The host tests used a public FatFs mirror whose `ff.c` identifies itself as
  "R0.16 w/patch 2", the version `dependencies.json` pins. Byte equality with the
  pinned archive could not be checked (elm-chan.org was unreachable from the test
  environment); CI's `host` job will be the first run on the real archive.

## M1.5 UI follow-up — 2026-09-23

A completed owner-supplied House of the Dead 2 capture on the first shell
(`24d5cfe735d7`) averaged **911.9 KiB/s**, captured all three tracks and matched
TOSEC using stream CRC32. UI scheduled time was **12.4%**, compared with about
4–5% in the accepted diagnostic UI runs. DMA remained active (15,795 chunks;
four PIO chunks), with CRC32, automatic readback Off and UI 2 Hz.

See the [sanitized results and source-log hash](evidence/m15-house-of-the-dead-2-2026-09-23.json).
The raw log is retained in the project conversation and is not published. This is an
ordinary completed capture supplied by the owner, not a new optical experiment.
At the time of that log, the restored-menu update (`8bae3efe7c2f`) and its optimized
framebuffer clear still awaited a console run. The subsequent completed MDK2
report now supplies that observation: **973.96 KiB/s**, all 31 tracks captured,
TOSEC FULL TRACK MATCH, CRC32, end readback Off and DMA. This is 3.73% below the
accepted same-disc Trip 12 rate, or 45.61 s more capture time. UI scheduled time
is 8.3%, compared with Trip 12's 4.9%; its additional 45.032 s nearly matches the
additional 45.936 s of operation wall time, supporting remaining UI overhead.
See [the sanitized MDK2 evidence](evidence/m15-mdk2-2026-09-23.json). UI time
overlaps stage timers, and the earlier 12.4% first-shell figure used another game.
Neither comparison isolates a single drawing cost. This ordinary completed rip
does not reopen reader experiments. Saved-file/PC checking of these particular
jobs remains separate from their captured-stream reference matches.

## Ripper controls and destinations — 2026-09-23

The next implementation selects an SD parent folder (default `/Games`), creates
title-numbered jobs with named GDI descriptors, and displays structured reference
results. Advanced groups Verify, Resume and Settings; a dedicated salvage flow
remains planned. See [ripper controls](ripper-controls.md).

This change does not alter the accepted acquisition strategy or start a new
optical experiment. Baseline `make test` and `make test-images` passed on clean
`54711b931554` before `capture.c` received limited destination, metadata and
result hooks. The raw/DMA reader, command state machine, retry policy and
checkpoint encoding remain unchanged. New FAT32/exFAT image cases pass for named
output, identity-based selection, collisions, invalid paths, metadata publication
failure/recovery and reference grades.

Hardware acceptance remains **one ordinary named capture**, its catalogue result
and PC saved-file verification, plus destination persistence and controls. The
same bootstrap disc is used. No speed improvement is attributed to this metadata
and UI work without corresponding hardware evidence.
