TPMJB/K-UI-NeXT/docs/capture-test.md

# First complete GDI capture test

This SD update implements M1.3 capture and M1.4 saved-file verification and
controlled resume. One physical capture and console reread have completed;
tracks 1 and 2 were independently checked on PC. Full PC/reference verification
remain pending. MDK2 now has logged checkpoint/prefix validation and new audio
writes after Resume in a fresh runtime session, followed by controlled Stop.
Final verification of a complete resumed hardware dump remains pending.
See [the evidence](hardware-evidence.md).
Keep the reusable bootstrap disc that already loads SD.

For the current MDK2 speed investigation, use the
[short optical timing test](optical-test.md). The isolated audio baseline is
complete; this update separates the optical operations and saves reports
automatically. The broader [performance plan](performance-test-plan.md) retains
the later optimization and fast-resume work.

## Install the update

1. Download **sd-update** from the successful Diagnostic build run. Keep a copy
   of your currently working `runtime.kui` on the PC.
2. With the console off, copy the download's `KUI/runtime.kui` to the card's
   `/KUI/runtime.kui`. Safely eject the card. Leave existing files in place.
3. Boot the **same existing CD**, without holding B. Confirm **SD runtime** and
   the new build ID. The capture page has **A New dump / X Resume / Y Verify**.
4. Replace the boot CD with a clean, known-good retail GD-ROM and close the lid.
   Start with an original well-kept game such as Evolution 2. Use the accessible
   exFAT card, with at least 1.5 GB free. No new CD burn is needed.

## Controls

| Control | Capture page | Diagnostics page |
| --- | --- | --- |
| A | New dump in a new directory | Disc sample probe |
| X | Resume newest job matching this disc | SD write/reread probe |
| Y | Verify newest completed job matching this disc | Save current log |
| B | Stop; finish/abort current call and checkpoint written data | Stop current probe |
| Left / Right | Switch pages while idle | Switch pages while idle |
| Up / Down | Scroll log | Scroll log |
| Start | Latest log lines | Latest log lines |
| Left trigger | mstats snapshot, also during capture | mstats snapshot |

The stick can also navigate. Input does not start another operation while one
is running. Wait for the operation to end and **READY** before removing the
card or powering off. A storage call may take time to return after Stop.

The RAM line updates once per second. Pull the left trigger at idle, during
track 3 and during verification to add detailed **mstats** snapshots to the log.
See [counter definitions and DreamShell comparison notes](memory-stats.md).

## Measure capture time

Each operation now appends a **TIMING** summary when it stops, fails or finishes.
For the current MDK2 test, resume its audio checkpoint and capture for about
60 seconds. Press B and release it, then wait for **Report saved** and **READY**.
Capture, Resume and Verify now save a fresh diagnostic report automatically
after completion, failure or Stop. If saving fails, diagnostics Y can retry.
The timing summary lives in that report, not the checkpoint. Existing jobs
can still resume with X after this SD update.
There is no need to interrupt an already running rip to install it.

The summary separates **setup**, **resume** prefix checking, **capture**,
**verify** saved-file rereading, and **finish** metadata publication. Within
each phase, `us` is elapsed microseconds, `pct` is that phase's wall-time share,
and `calls` is the number of measured operations. Use the `sha256` percentage
under **capture** to assess hashing during ripping; the later SD reread has
its own SHA-256 percentage. A Stop summary measures just that operation's work.

| Category | What its elapsed time includes |
| --- | --- |
| disc | The raw-read callback: both guarded PIO reads, mode setup, polling/waits, buffer checks and comparison; retries are timed too |
| edc | Data-sector layout and EDC validation |
| write / read | Track-file FatFs write / read calls, including their allocation and buffering work |
| sha256 / crc32 | Track hash processing; final SHA-256 digests during prefix/full rereading also count |
| checkpoint | Track sync, checkpoint hash finalization/encoding, metadata writes, sync and close; these are not counted again in the other categories |
| other | Remaining work, including file open/close, progress updates, and work between measured calls |

`bytes` counts logical bytes for successful disc/track I/O calls, bytes passed
to each hash, bytes in sectors checked for EDC, or saved checkpoint records.
A paired disc request counts its logical data once. Failed/short I/O contributes
time and calls but zero bytes; successful retries can contribute repeated bytes.
Final SHA digests contribute time/calls but zero additional input bytes.

These are **wall-clock measurements**, including scheduling delays, not isolated
CPU-cycle counts. They include timer overhead and are not a direct prediction of
speed with a feature removed. Counters use KOS's 64-bit microsecond timer and
fixed memory; they add no per-chunk log or SD writes. This update keeps the paired
reads, hashes, validation, checkpoint interval and on-card formats unchanged.
The added `TRACK` and `OPTICAL` summaries break down capture tracks and raw-read
work; their nested timer levels are explained in [the optical test](optical-test.md).
Automatic reports use a fresh probe directory and a temporary file, publishing
`diagnostics.txt` only after write/sync/close. Their I/O runs after capture ends,
outside the timing totals. A log-save failure does not change the capture result.
Even a refused capture/verify can write this separate report; it does not modify
the rejected capture's track or checkpoint files.
Measurement begins after initial TOC preparation and SD connection; the setup
phase covers disc fingerprinting and filesystem/job preparation within capture.

## One combined capture/resume test

1. Press A on the capture page. It reads both TOCs and content samples, checks
   available space, and creates `/KUI/dumps/d<identity-prefix>-0001/` (or the next
   unused number). It displays the title, profile and selected track ranges.
2. Once writing has progressed into track 3, press B. Wait for **STOPPED** and
   **READY**. Note the last committed byte count and job directory.
3. For the first resume check, power off normally. Reinsert the same bootstrap
   CD, boot the SD runtime, then swap back to the **same game disc**. Press X.
   It should select the same job, validate both checkpoints, and reread all
   committed bytes before continuing. This prefix check is expected to take time.
4. Let it finish. Capture is followed by a complete SD reread. The success line
   must say **SAVED DATA VERIFIED** and give the output `disc.gdi` path. A failure,
   Stop, or **Capture written** alone is not completion. If `KUI/redump.db` or
   `KUI/tosec.db` is on the card, a `Reference check` line before the path says
   how the finished capture compares with the known-good Redump/TOSEC CRCs
   (`FULL TRACK MATCH` is the best result; no match is inconclusive, not a failure).
5. Wait for the automatically saved report path and READY, then power off and
   retrieve the job's `manifest.json`, `disc.gdi`, and that diagnostic log.
   Diagnostics Y remains available for a manual report or retry.

Do not press A to resume: A deliberately creates a separate new job. X chooses
the newest directory for the current content fingerprint; it does not silently
fall back to an older job if that newest job's checkpoints are invalid. A new
complete rip can later provide the uninterrupted-versus-resumed comparison.

If the disc errors, the job stops after its retry budget and retains committed
data. The screen gives the track/FAD and drive sense information. After cleaning
or reinserting the same disc, X re-identifies it before writing. If an abort
cannot be confirmed or a buffer guard fails, reset the console first. There is
no zero-fill completion path and no claimed damaged-disc recovery rate.

## Check on the computer

The download includes a Python standard-library verifier. Point it at the
directory containing the completed tracks, `disc.gdi` and `manifest.json`:

```sh
python3 verify_dump.py /path/to/card/KUI/dumps/d0123456789abcdef-0001
```

It independently checks every track's length, CRC32, SHA-256 and GDI layout.
No reference comparison is claimed by default. To compare with an independently
verified reference manifest using the same track/gap convention:

```sh
python3 verify_dump.py /path/to/dump --reference /path/to/reference.json
```

A reference needs `profile: "gdi-raw2352-typegap150-v1"` and a `tracks` array
containing each required `file`, `bytes`, and `crc32` and/or `sha256`. A missing
track produces **PARTIAL MATCH ONLY** (exit 2); a mismatch produces exit 1.
All provided hashes must agree. Do not label an old dump as this profile until
its track sizes and gap convention have been checked. No catalog is bundled.

Send the build ID, disc title/region, manifest, GDI, diagnostic log and verifier
output. The full raw track files need not be uploaded. Note capture speed and
whether Stop, reboot, resume and final verification worked.

## Limits of this first capture update

- One physical capture has completed; full PC/reference verification remains
  pending. Build `2657a97031e3` showed about 209-220 KiB/s during capture.
  Each raw request is read twice with different initial fills and compared.
  This favors detecting
  underfilled/unstable buffers at a potential speed cost.
- Data sectors require a supported Mode 1/Mode 2 Form 1 layout and valid EDC.
  ECC correction, subchannels and audio-offset correction are not implemented.
- The [documented GDI profile](capture-format.md) excludes 150 sectors before
  an intra-session audio/data type change. TOCs do not measure arbitrary INDEX
  00 boundaries. A reference match still needs an independent compatible dump.
- Checkpoints support controlled Stop/Resume and validate saved data before
  appending. FAT/exFAT and card firmware do not guarantee arbitrary power-loss
  recovery. Use the controlled Stop test first.
- Resume is limited to the newest job for the current disc fingerprint.
  Existing completed jobs remain untouched when starting another dump.

Holding B at boot still uses your original CD fallback. Ordinary capture fixes
can be distributed as another `runtime.kui` using that same disc.
