TPMJB/K-UI-NeXT/docs/evidence/sci-dma-cached-quick-2026-10-01-result.csv

id | build | card_label | transport | filesystem | cluster_bytes | music_playing | ui_hz | preset | outcome | repeat | chunk_bytes | bytes | write_us | read_us | sync_us | verified
5 | a6cb21895c37 | sci dma | 1 | exFAT | 131072 | 0 | 2 | 0 | 2 | 1 | 65536 | 4194304 | 3708977 | 3890856 | 8554 | 1
