TPMJB/K-UI-NeXT/docs/evidence/sci-dma-profile-2026-10-01-quick-result.csv

id | build | card_label | transport | filesystem | cluster_bytes | music_playing | ui_hz | preset | outcome | repeat | chunk_bytes | bytes | write_us | read_us | sync_us | verified
6 | 65fcaafadb98 | sci dma2 | 1 | exFAT | 131072 | 0 | 2 | 0 | 2 | 1 | 65536 | 4194304 | 3732398 | 3949736 | 5813 | 1
