TPMJB/K-UI-NeXT/docs/evidence/sci-dma-profile-2026-10-01-soak-result.csv

id | build | card_label | transport | filesystem | cluster_bytes | music_playing | ui_hz | preset | outcome | repeat | chunk_bytes | bytes | write_us | read_us | sync_us | verified
7 | 65fcaafadb98 | sci dma2 | 1 | exFAT | 131072 | 0 | 2 | 2 | 2 | 1 | 65536 | 167772160 | 144658030 | 156894349 | 81947 | 1
