TPMJB/K-UI-NeXT/docs/evidence/sci-dma-soak-2026-10-01-result.csv

id | build | card_label | transport | filesystem | cluster_bytes | music_playing | ui_hz | preset | outcome | repeat | chunk_bytes | bytes | write_us | read_us | sync_us | verified
4 | cf8e7ea7866b | sci | 1 | exFAT | 131072 | 0 | 2 | 2 | 2 | 1 | 65536 | 436207616 | 424025226 | 459968795 | 148419 | 1
