TPMJB/K-UI-NeXT/docs/evidence/sci-dma-word-soak-2026-10-01-result.csv

id | build | card_label | transport | filesystem | cluster_bytes | music_playing | ui_hz | preset | outcome | repeat | chunk_bytes | bytes | write_us | read_us | sync_us | verified
8 | 499bcb53c2d4 |  | 1 | exFAT | 131072 | 0 | 2 | 2 | 2 | 1 | 65536 | 167772160 | 136916577 | 156202570 | 101296 | 1
