TPMJB/K-UI-NeXT/docs/evidence/sci-game-pacing-result-2026-10-01.csv

id | build | card_label | transport | filesystem | cluster_bytes | music_playing | ui_hz | preset | outcome | repeat | chunk_bytes | bytes | write_us | read_us | sync_us | verified
13 | 8d930310f79d |  | 1 | exFAT | 131072 | 0 | 2 | 2 | 2 | 1 | 65536 | 167772160 | 136829789 | 153842778 | 93720 | 1
