TPMJB/K-UI-NeXT/include/kui/shell.h

/* SPDX-License-Identifier: GPL-3.0-only */
#ifndef KUI_SHELL_H
#define KUI_SHELL_H
#include "kui/settings.h"
#include "kui/destination.h"
#include "kui/known_dumps.h"
#include "kui/system_settings.h"
#include "kui/apps.h"
#include "kui/music_player.h"
#include "kui/clock.h"
#include "kui/cd_audio.h"
#include "kui/games.h"
#include "kui/games_covers.h"
#include "kui/files.h"
#include "kui/ftp.h"
#include "kui/storage_test.h"
#include "kui/network_wifi.h"
#include <stdbool.h>
#include <stdint.h>

#define KUI_SHELL_WIDTH 640u
#define KUI_SHELL_HEIGHT 480u
#define KUI_SHELL_LOG_ROWS 10u
/* A cover belongs to one published listing and selection. The worker must
 * echo this key; main publishes pixels only after the same key is accepted. */
struct kui_shell_games_art_key {
    unsigned generation,page,view,row;
    char root[KUI_DEST_ROOT_CAP],path[KUI_GAMES_FILE_CAP];
};
enum kui_shell_button {
    KUI_SHELL_UP = 1u << 0, KUI_SHELL_DOWN = 1u << 1,
    KUI_SHELL_LEFT = 1u << 2, KUI_SHELL_RIGHT = 1u << 3,
    KUI_SHELL_A = 1u << 4, KUI_SHELL_B = 1u << 5,
    KUI_SHELL_X = 1u << 6, KUI_SHELL_Y = 1u << 7,
    KUI_SHELL_START = 1u << 8, KUI_SHELL_L = 1u << 9,
    KUI_SHELL_R = 1u << 10
};
enum kui_shell_page { KUI_SHELL_HOME, KUI_SHELL_RIPPER,
    KUI_SHELL_SETTINGS, KUI_SHELL_DIAGNOSTICS,
    KUI_SHELL_DESTINATION, KUI_SHELL_KEYBOARD, KUI_SHELL_ADVANCED,
    KUI_SHELL_RIPPER_SETTINGS, KUI_SHELL_VMU, KUI_SHELL_MEMORY, KUI_SHELL_NETWORK,
    KUI_SHELL_GD_PLAY, KUI_SHELL_MUSIC, KUI_SHELL_CLOCK,
    KUI_SHELL_VMU_RESTORE, KUI_SHELL_CRC_SCAN, KUI_SHELL_VMU_ACTIONS, KUI_SHELL_SYSTEM_TOOLS, KUI_SHELL_SALVAGE, KUI_SHELL_CD_AUDIO,
    KUI_SHELL_GAMES, KUI_SHELL_GAMES_DETAIL, KUI_SHELL_GAMES_ADVANCED,
    KUI_SHELL_GAMES_PROBE_CONFIRM, KUI_SHELL_GAMES_IMAGE_PROBE_CONFIRM,
    KUI_SHELL_GAMES_RETAIL_CONFIRM,
    KUI_SHELL_FILES, KUI_SHELL_FILES_ACTIONS, KUI_SHELL_FILES_PICK,
    KUI_SHELL_FILES_CONFIRM, KUI_SHELL_FILES_INFO, KUI_SHELL_FILES_VIEW,
    KUI_SHELL_FTP, KUI_SHELL_STORAGE_TESTS, KUI_SHELL_STORAGE_TEST_HISTORY,
    KUI_SHELL_SCI_ASYNC_PROBE, KUI_SHELL_GAMES_VARIANTS, KUI_SHELL_WIFI };
enum kui_shell_action {
    KUI_SHELL_NONE, KUI_SHELL_STOP, KUI_SHELL_MSTATS,
    KUI_SHELL_DISC_PROBE, KUI_SHELL_STORAGE_PROBE, KUI_SHELL_SAVE_LOG,
    KUI_SHELL_NEW_DUMP, KUI_SHELL_RESUME, KUI_SHELL_VERIFY,
    KUI_SHELL_BENCH, KUI_SHELL_LOAD_SETTINGS, KUI_SHELL_SAVE_SETTINGS,
    KUI_SHELL_DISCARD_SETTINGS, KUI_SHELL_DEST_LIST, KUI_SHELL_DEST_SAVE,
    KUI_SHELL_MEMORY_TEST, KUI_SHELL_NETWORK_TEST, KUI_SHELL_VMU_LIST,
    KUI_SHELL_VMU_BACKUP, KUI_SHELL_VMU_BACKUP_ALL, KUI_SHELL_LOAD_SYSTEM,
    KUI_SHELL_SAVE_SYSTEM, KUI_SHELL_DISCARD_SYSTEM, KUI_SHELL_PREVIEW_VIDEO,
    KUI_SHELL_CONFIRM_VIDEO, KUI_SHELL_CANCEL_VIDEO, KUI_SHELL_MUSIC_NEXT,
    KUI_SHELL_MUSIC_CYCLE, KUI_SHELL_RESUME_QUICK, KUI_SHELL_GD_BOOT,
    KUI_SHELL_MUSIC_LIST, KUI_SHELL_MUSIC_PLAY,
    KUI_SHELL_MUSIC_PREVIOUS, KUI_SHELL_MUSIC_STOP,
    KUI_SHELL_CLOCK_READ, KUI_SHELL_CLOCK_WRITE, KUI_SHELL_VMU_BACKUPS_LIST,
    KUI_SHELL_VMU_RESTORE_PREVIEW, KUI_SHELL_VMU_RESTORE_COMMIT, KUI_SHELL_ADVANCED_CRC,
    KUI_SHELL_VMU_DELETE_PREVIEW, KUI_SHELL_VMU_DELETE_COMMIT,
    KUI_SHELL_VMU_COPY_PREVIEW, KUI_SHELL_VMU_COPY_COMMIT, KUI_SHELL_MUSIC_CLEAR_CACHE,
    KUI_SHELL_NETWORK_CONNECT, KUI_SHELL_SYSTEM_INSPECT, KUI_SHELL_FLASH_BACKUP,
    KUI_SHELL_BIOS_BACKUP, KUI_SHELL_RESTART,
    KUI_SHELL_SALVAGE_NEW, KUI_SHELL_SALVAGE_RESUME, KUI_SHELL_SALVAGE_RECOVER,
    KUI_SHELL_CD_LIST, KUI_SHELL_CD_PLAY, KUI_SHELL_CD_PAUSE, KUI_SHELL_CD_RESUME, KUI_SHELL_CD_STOP,
    KUI_SHELL_GAMES_LIST, KUI_SHELL_GAMES_INSPECT, KUI_SHELL_GAMES_PROBE,
    KUI_SHELL_GAMES_IMAGE_PROBE, KUI_SHELL_GAMES_RETAIL, KUI_SHELL_GAMES_SCAN,
    KUI_SHELL_FILES_LIST, KUI_SHELL_FILES_CHECK, KUI_SHELL_FILES_RUN, KUI_SHELL_FILES_PICTURE,
    KUI_SHELL_FTP_START, KUI_SHELL_TEST_RUN, KUI_SHELL_TEST_HISTORY,
    KUI_SHELL_TEST_BASELINE, KUI_SHELL_SCI_ASYNC_RUN, KUI_SHELL_SCI_ASYNC_STRESS,
    KUI_SHELL_SCI_ASYNC_SCREEN, KUI_SHELL_SCI_ASYNC_SPEED,
    KUI_SHELL_WIFI_REFRESH, KUI_SHELL_WIFI_JOIN, KUI_SHELL_WIFI_FORGET,
    KUI_SHELL_WIFI_BAND
};
enum kui_shell_outcome { KUI_SHELL_OUTCOME_NONE, KUI_SHELL_OUTCOME_COMPLETE,
    KUI_SHELL_OUTCOME_STOPPED, KUI_SHELL_OUTCOME_FAILED };
struct kui_shell {
    enum kui_shell_page page;
    unsigned home_selected, setting_selected, scroll;
    bool confirm_new, confirm_quick_resume, confirm_gd_boot;
    struct kui_settings saved, draft;
    struct kui_system_settings system_saved, system_draft;
    unsigned system_selected;
    bool video_trial, confirm_defaults, confirm_clock, confirm_vmu_restore;
    bool confirm_vmu_delete, confirm_vmu_copy, confirm_music_clear, confirm_restart;
    unsigned tools_selected;
    bool confirm_salvage, salvage_zero_fill;
    unsigned salvage_selected, salvage_passes;
    unsigned vmu_action_selected, vmu_copy_slot;
    bool clock_valid;
    unsigned clock_selected;
    struct kui_datetime clock_draft;
    char clock_notice[128];
    unsigned vmu_slot, vmu_page, vmu_selected;
    struct kui_vmu_view vmu;
    struct kui_vmu_backup_view backups;
    unsigned backup_page, backup_selected;
    char restore_path[KUI_VMU_BACKUP_PATH_CAP], restore_name[16];
    uint32_t restore_bytes;
    char music_path[KUI_DEST_ROOT_CAP], music_selected_path[KUI_DEST_ROOT_CAP];
    unsigned music_page, music_selected;
    struct kui_music_player_page music_listing;
    struct kui_cd_audio_status cd_audio;
    unsigned cd_selected;
    char games_path[KUI_DEST_ROOT_CAP], games_selected_path[KUI_GAMES_FILE_CAP];
    /* A paired game keeps both exact files while details/confirmation are
     * open; the selected path is set only after the version is chosen. */
    char games_original_path[KUI_GAMES_FILE_CAP], games_2048_path[KUI_GAMES_FILE_CAP];
    unsigned games_variant_selected;
    unsigned games_page, games_selected, games_advanced_selected;
    /* KUI_GAMES_VIEW_SAVED until a listing reports the card's saved view. */
    unsigned games_view;
    unsigned games_generation;
    bool games_loading,games_art_loading;
    bool games_scanning; /* The box art scan runs; a listing ends it. */
    /* Explicit refresh rebuilds worker-owned directory discovery; entering,
     * page and view changes reuse its read-only snapshot. */
    bool games_refresh;
    /* The launch's reader (enum kui_retail_reader): A launches with the
     * standard one, X with the background SCI reader under test. */
    unsigned games_retail_reader;
    bool games_retail_scrambled; /* Native CD boot encoding chosen at confirmation. */
    struct kui_games_page games_listing;
    struct kui_games_detail games_detail;
    /* Destination is committed only by a successful worker load/save. Browsing
     * and typing are drafts; neither changes where a new capture is written. */
    char destination[KUI_DEST_ROOT_CAP], browse_path[KUI_DEST_ROOT_CAP];
    char keyboard[KUI_DEST_ROOT_CAP], keyboard_original[KUI_DEST_ROOT_CAP];
    char destination_notice[128];
    struct kui_destination_page listing;
    unsigned browser_selected, browser_page, keyboard_selected;
    unsigned advanced_selected;
    enum kui_shell_page settings_return;
    unsigned keyboard_layer; /* KUI_SHELL_KEYS_* */
    bool browse_for_scan;
    /* File Manager. files_request is the next listing main hands to the
     * worker: the browser's folder, or the picker's (folders_only). A job
     * is checked (FILES_CHECK) before it is confirmed and run (FILES_RUN);
     * the run is followed by files_request, which lists the folder again. */
    char files_path[KUI_FILES_PATH_CAP], files_pick_path[KUI_FILES_PATH_CAP];
    struct kui_files_page files_listing, files_pick;
    struct kui_files_request files_request;
    struct kui_files_job files_job;
    struct kui_files_preview files_preview;
    struct kui_files_picture files_picture;
    unsigned files_selected, files_pick_selected, files_action_selected;
    char files_notice[128], files_notice_detail[KUI_APP_LINE_CAP];
    /* The keyboard types a File Manager name; Games details were opened
     * from the File Manager, so B returns there. */
    bool files_keyboard, files_notice_error, games_from_files;
    /* A copy, move, delete, rename or new folder runs until its status is
     * installed; the browser shows its progress meanwhile. */
    bool files_running;
    /* Diagnostics' storage tests use worker-published copies only. The last
     * request stays independent of whichever historical result is displayed. */
    struct kui_storage_test_request storage_test_request, storage_test_last_request;
    struct kui_storage_test_result storage_test_result;
    struct kui_storage_test_history storage_test_history;
    unsigned storage_test_selected, storage_history_selected, storage_test_chunk;
    uint32_t storage_test_baseline_id;
    bool storage_test_last_valid, storage_test_show_result, storage_test_details;
    bool storage_test_from_history, storage_test_keyboard, confirm_storage_test;
    /* The Wi-Fi page: the board's latest view; rows are the band setting,
     * the networks in range, then "Other network". wifi_request is the job
     * main hands to the worker (JOIN, BAND); main wipes its password once
     * taken. The keyboard types the password, or first the name of a
     * network typed by hand (wifi_typing_name). */
    struct kui_wifi_view wifi;
    unsigned wifi_selected;
    struct kui_wifi_request wifi_request;
    uint8_t wifi_security; /* of the network being joined; 0xff: not known */
    bool wifi_keyboard, wifi_typing_name, confirm_wifi_forget;
};
/* Home's apps, top to bottom: A on row home_selected opens
 * kui_shell_home_pages[home_selected]. Drawing looks each app up by page. */
#define KUI_SHELL_HOME_APPS 10u
extern const enum kui_shell_page kui_shell_home_pages[KUI_SHELL_HOME_APPS];
void kui_shell_init(struct kui_shell *shell, const struct kui_settings *settings);
/* Main owns the reducer. Pass new button edges; a held B must also be included
 * when another edge arrives, so Stop/cancel retains priority over a new action.
 * Busy includes queued work and settings I/O, not background audio playback.
 * It locks launch/navigation but permits Stop, song requests on Home/Ripper,
 * memory snapshots and scrolling the diagnostics already open. Song requests
 * do not grant the renderer/reducer access to the filesystem. */
enum kui_shell_action kui_shell_input(struct kui_shell *shell,
    unsigned pressed, bool busy);
/* Install only a successfully loaded/saved settings snapshot. A failed save
 * leaves draft values available for retry and the prior saved values intact. */
void kui_shell_set_preferences(struct kui_shell *shell,
    const struct kui_settings *settings);
bool kui_shell_settings_dirty(const struct kui_shell *shell);
void kui_shell_set_system_preferences(struct kui_shell *shell,
    const struct kui_system_settings *settings);
bool kui_shell_system_dirty(const struct kui_shell *shell);
/* Main controls video_trial only while its reversible platform preview is
 * active. The reducer returns CONFIRM/CANCEL; it never commits a video mode. */
void kui_shell_set_vmu(struct kui_shell *shell, const struct kui_vmu_view *view);
/* Worker publications are ignored unless their page/slot still matches. */
void kui_shell_set_vmu_backups(struct kui_shell *shell, const struct kui_vmu_backup_view *view);
void kui_shell_set_vmu_restore_preview(struct kui_shell *shell, const struct kui_vmu_view *view);
/* A successful clock read or write replaces the editable snapshot. Failure
 * preserves a valid draft or seeds an editable 1980-01-01 with an error notice. */
void kui_shell_set_vmu_delete_preview(struct kui_shell *shell, const struct kui_vmu_view *view);
void kui_shell_set_vmu_copy_preview(struct kui_shell *shell, const struct kui_vmu_view *view);
void kui_shell_set_clock(struct kui_shell *shell, const struct kui_datetime *value, const char *notice);
/* MUSIC_LIST uses music_path and music_page * ROWS. MUSIC_PLAY uses the
 * validated music_selected_path. Worker completion never changes directory. */
void kui_shell_set_cd_audio(struct kui_shell *shell, const struct kui_cd_audio_status *status);
void kui_shell_set_music_listing(struct kui_shell *shell,
    const struct kui_music_player_page *page);
/* Games results must still match their active page and requested root/path.
 * Main also checks worker generation to reject stale same-folder pagination.
 * LIST uses games_path + games_page * ROWS and games_view; INSPECT uses
 * games_selected_path. SCAN covers /Games, then lists its first page. */
void kui_shell_set_games_listing(struct kui_shell *shell, const struct kui_games_page *page);
/* Worker publications must match the request that is still on screen. */
bool kui_shell_set_games_rows(struct kui_shell *,const struct kui_games_page *,
    unsigned generation,unsigned offset,unsigned requested_view);
void kui_shell_set_games_detail(struct kui_shell *shell, const struct kui_games_detail *detail);
bool kui_shell_games_image_ready(const struct kui_shell *shell);
/* The view to draw: the saved view once known, else the list. */
unsigned kui_shell_games_view(const struct kui_shell *shell);
bool kui_shell_games_art_key(const struct kui_shell *,struct kui_shell_games_art_key *);
bool kui_shell_games_art_same(const struct kui_shell_games_art_key *,const struct kui_shell_games_art_key *);
bool kui_shell_set_games_art(struct kui_shell *,const struct kui_shell_games_art_key *,
    const struct kui_games_cover_result *);
/* Selected paired version, or NULL for an ordinary single image. */
const char *kui_shell_games_variant_label(const struct kui_shell *shell);
/* Exact initial test profile only; preparation revalidates files and metadata. */
bool kui_shell_games_retail_ready(const struct kui_shell *shell);
bool kui_shell_games_encoding_ready(const struct kui_shell *shell);
/* A Windows CE image the CE boot test can take: it loads the CE kernel,
 * starts it, and stops at the first disc request K-UI cannot serve. */
bool kui_shell_games_ce_probe_ready(const struct kui_shell *shell);
/* File Manager results. A listing is kept only for the folder it was asked
 * for; a check only for the job and page that asked; a picture only while
 * its view is open. A run's status becomes the browser's notice. */
void kui_shell_set_files_listing(struct kui_shell *shell, const struct kui_files_page *page);
void kui_shell_set_files_preview(struct kui_shell *shell, const struct kui_files_preview *preview);
void kui_shell_set_files_status(struct kui_shell *shell, const struct kui_app_status *status);
void kui_shell_set_files_picture(struct kui_shell *shell, const struct kui_files_picture *picture);
/* TEST_RUN consumes storage_test_request; TEST_BASELINE consumes the selected
 * saved passing storage_test_baseline_id. Publications contain no borrowed
 * pointers and are installed on main's reducer thread after worker completion. */
void kui_shell_set_storage_test_result(struct kui_shell *shell,
    const struct kui_storage_test_result *result);
void kui_shell_set_storage_test_history(struct kui_shell *shell,
    const struct kui_storage_test_history *history);
/* The job may be confirmed: its check succeeded and still matches. */
bool kui_shell_files_ready(const struct kui_shell *shell);
/* DEST_LIST reads browse_path and browser_page (offset = page * PAGE_SIZE).
 * DEST_SAVE reads browse_path. Main owns the generation check before installing
 * worker results; these functions themselves perform no filesystem I/O. */
void kui_shell_set_destination(struct kui_shell *shell, const char *path);
void kui_shell_set_listing(struct kui_shell *shell,
    const struct kui_destination_page *page);
void kui_shell_destination_error(struct kui_shell *shell, const char *message);
/* Keyboard has four QWERTY/digit rows of ten keys, then SPACE/BACK/DONE.
 * Only directions may be repeated; A and the other action buttons are edges.
 * Y cycles its layers: lowercase, uppercase, then symbols. */
#define KUI_SHELL_KEY_COUNT 43u
enum { KUI_SHELL_KEYS_LOWER, KUI_SHELL_KEYS_UPPER, KUI_SHELL_KEYS_SYMBOLS, KUI_SHELL_KEY_LAYERS };
const char *kui_shell_key_label(unsigned key, unsigned layer);
/* The Wi-Fi page's view from the worker. A view without a scan keeps the
 * networks already listed. */
void kui_shell_set_wifi(struct kui_shell *shell, const struct kui_wifi_view *view);
/* Rows on the Wi-Fi page: the band setting, each network, "Other network". */
unsigned kui_shell_wifi_rows(const struct kui_shell *shell);

/* Main copies shared worker state while locked, then draws outside the lock.
 * Pointer fields remain valid for this draw. log_lines contains up to LOG_ROWS
 * already-scrolled lines; total_log_lines is the count before windowing.
 * phase uses the existing kui_capture_phase numeric values (0..4); phase 4 is
 * completed, never an assertion that saved bytes were verified. */
struct kui_shell_view {
    bool sci_video_quiet;
    const char *build, *job_dir, *message, *settings_notice;
    const char *disc_title, *inserted_title, *gdi_name;
    const char *music_title, *music_notice;
    const struct kui_app_status *app_status;
    bool busy, saving, cancel_requested, saved_verified, memory_valid;
    bool log_truncated, reference_checked, video_trial, drive_reset_required;
    bool dma_degraded;
    bool music_enabled, music_playing, music_paused, music_change_pending;
    unsigned music_volume;
    uint32_t music_cache_bytes, music_loading_bytes, music_peak_file_bytes;
    unsigned video_seconds;
    struct kui_known_summary reference;
    enum kui_shell_outcome outcome;
    unsigned phase, track, tracks, rate_kib, retries;
    unsigned retry_attempt, retry_limit;
    uint32_t retry_fad;
    uint64_t done, total, committed, elapsed_ms;
    uint64_t phase_elapsed_ms, progress_age_ms;
    uint32_t memory_used, memory_physical, memory_peak;
    const char *const *log_lines;
    unsigned log_count, total_log_lines;
    /* Games rows' covers, in the listing's view size (games_listing.view),
     * and image details' large cover. Valid only where the listing or
     * detail says cover; NULL draws placeholders. */
    const uint16_t (*game_covers)[KUI_COVER_PIXELS];
    /* Runtime keeps one selected cover; host previews may still supply rows. */
    const uint16_t *game_selected_cover;
    const uint16_t *game_detail_cover;
    /* The File Manager's picture, KUI_FILES_PICTURE_EDGE square; drawn only
     * while shell->files_picture says it loaded. */
    const uint16_t *files_picture;
    /* The FTP server's last published status, on its page; NULL before the
     * first start. */
    const struct kui_ftp_status *ftp;
    const struct kui_storage_test_progress *storage_test_progress;
    const char *storage_test_target;
};
/* Estimate only the current moving phase after a 2s warmup; do not imply the
 * later verification duration. A stalled (>3s old) rate is not an estimate. */
/* Tenths of a percent, clamped; zero for an unknown total. */
unsigned kui_shell_progress_tenths(uint64_t done, uint64_t total);
bool kui_shell_phase_eta(const struct kui_shell_view *view, uint64_t *seconds);
/* The renderer draws its embedded font and original artwork directly. Text is
 * clipped to safe margins. An optional observer receives rendered labels for
 * accessibility/host checks; it must not draw a second font over them. No flip,
 * wait, device access or allocation occurs here. */
typedef void (*kui_shell_text_fn)(void *ctx, unsigned x, unsigned y,
    uint16_t rgb565, const char *text, bool large);
void kui_shell_draw(uint16_t *frame, const struct kui_shell *shell,
    const struct kui_shell_view *view, kui_shell_text_fn text, void *ctx);
/* Console path: the caller first clears its offscreen framebuffer to RGB565
 * 0x0864 with KOS vid_clear(8,15,35). Keeping that optimized store-queue clear
 * outside the portable renderer avoids 307,200 ordinary CPU pixel stores. */
void kui_shell_draw_content(uint16_t *frame, const struct kui_shell *shell,
    const struct kui_shell_view *view, kui_shell_text_fn text, void *ctx);
#endif
