TPMJB/K-UI-NeXT/src/core/shell.c

/* SPDX-License-Identifier: GPL-3.0-only */
#include "kui/shell.h"
#include "kui/retail_image.h"
#include "kui/games_retail.h"
#include <limits.h>
#include <stdio.h>
#include <string.h>

const enum kui_shell_page kui_shell_home_pages[KUI_SHELL_HOME_APPS]={KUI_SHELL_GAMES,KUI_SHELL_RIPPER,
    KUI_SHELL_VMU,KUI_SHELL_FILES,KUI_SHELL_MUSIC,KUI_SHELL_GD_PLAY,KUI_SHELL_MEMORY,KUI_SHELL_NETWORK,
    KUI_SHELL_DIAGNOSTICS,KUI_SHELL_SETTINGS};
void kui_shell_set_preferences(struct kui_shell *s, const struct kui_settings *p) {
    if(!s || !p) return;
    s->saved = *p;
    if((unsigned)s->saved.capture_format>=KUI_CAPTURE_FORMAT_COUNT) s->saved.capture_format=KUI_CAPTURE_FORMAT_GDI;
    if(!s->saved.crc_only) s->saved.end_readback = true;
    s->draft = s->saved;
}
void kui_shell_init(struct kui_shell *s, const struct kui_settings *p) {
    if(!s) return;
    memset(s, 0, sizeof(*s));
    s->salvage_passes=1;
    kui_storage_test_defaults(&s->storage_test_request);
    const struct kui_settings initial = {true, false, true,KUI_CAPTURE_FORMAT_GDI};
    kui_shell_set_preferences(s, p ? p : &initial);
    kui_system_settings_default(&s->system_saved);
    s->system_draft=s->system_saved;
    snprintf(s->music_path,sizeof(s->music_path),"/Music");
    snprintf(s->games_path,sizeof(s->games_path),"/Games");
    s->games_view=KUI_GAMES_VIEW_SAVED;
    snprintf(s->files_path,sizeof(s->files_path),"/");
    kui_destination_default(s->destination);
    memcpy(s->browse_path,s->destination,sizeof(s->browse_path));
}
void kui_shell_set_system_preferences(struct kui_shell *s,const struct kui_system_settings *p) {
    if(!s || !p || !kui_system_settings_valid(p)) return;
    s->system_saved=*p; s->system_draft=*p;
}
bool kui_shell_system_dirty(const struct kui_shell *s) {
    return s && (s->system_saved.video_mode!=s->system_draft.video_mode ||
        s->system_saved.show_memory!=s->system_draft.show_memory ||
        s->system_saved.music_enabled!=s->system_draft.music_enabled ||
        s->system_saved.music_volume!=s->system_draft.music_volume ||
        s->system_saved.startup_chime!=s->system_draft.startup_chime ||
        s->system_saved.startup_app!=s->system_draft.startup_app ||
        s->system_saved.screen_inset!=s->system_draft.screen_inset ||
        s->system_saved.menu_sounds!=s->system_draft.menu_sounds);
}
void kui_shell_set_vmu(struct kui_shell *s,const struct kui_vmu_view *view) {
    if(!s || !view || view->slot!=s->vmu_slot || view->page!=s->vmu_page) return;
    s->vmu=*view;
    if(s->vmu.count>KUI_VMU_ROWS) s->vmu.count=KUI_VMU_ROWS;
    for(unsigned i=0;i<s->vmu.count;i++) s->vmu.entries[i].name[sizeof(s->vmu.entries[i].name)-1]=0;
    if(s->vmu_selected>=s->vmu.count) s->vmu_selected=0;
}
void kui_shell_set_vmu_backups(struct kui_shell *s,const struct kui_vmu_backup_view *view) {
    if(!s || !view || s->page!=KUI_SHELL_VMU_RESTORE || view->page!=s->backup_page) return;
    s->backups=*view;
    s->backups.status.message[sizeof(s->backups.status.message)-1]=0;
    if(s->backups.count>KUI_VMU_ROWS) s->backups.count=KUI_VMU_ROWS;
    for(unsigned i=0;i<s->backups.count;i++) {
        struct kui_vmu_backup_entry *e=&s->backups.entries[i];
        e->name[sizeof(e->name)-1]=0;e->folder[sizeof(e->folder)-1]=0;
        /* An unterminated path is unusable, never silently truncated. */
        if(!memchr(e->path,0,sizeof(e->path))) e->path[0]=0;
    }
    if(s->backup_selected>=s->backups.count) s->backup_selected=0;
}
void kui_shell_set_vmu_restore_preview(struct kui_shell *s,const struct kui_vmu_view *view) {
    if(!s || !view || s->page!=KUI_SHELL_VMU_RESTORE || view->slot!=s->vmu_slot) return;
    s->backups.status=view->status;
    s->backups.status.message[sizeof(s->backups.status.message)-1]=0;
    s->confirm_vmu_restore=view->restore_ready && s->restore_path[0] && view->count &&
        memchr(view->entries[0].name,0,sizeof(view->entries[0].name));
    if(s->confirm_vmu_restore) {
        /* Display the save that was actually checked, not stale browser text. */
        snprintf(s->restore_name,sizeof(s->restore_name),"%s",view->entries[0].name);
        s->restore_bytes=view->entries[0].bytes;
    }
}
void kui_shell_set_vmu_delete_preview(struct kui_shell *s,const struct kui_vmu_view *view) {
    if(!s || !view || s->page!=KUI_SHELL_VMU_ACTIONS || view->slot!=s->vmu_slot) return;
    s->vmu.status=view->status;
    s->vmu.status.message[sizeof(s->vmu.status.message)-1]=0;
    s->confirm_vmu_delete=view->delete_ready && s->vmu_action_selected==0 && view->count &&
        s->vmu_selected<s->vmu.count && memchr(view->entries[0].name,0,sizeof(view->entries[0].name));
    if(s->confirm_vmu_delete) s->vmu.entries[s->vmu_selected]=view->entries[0];
    else if(view->status.complete) s->vmu.count=0;
}
void kui_shell_set_vmu_copy_preview(struct kui_shell *s,const struct kui_vmu_view *view) {
    if(!s || !view || s->page!=KUI_SHELL_VMU_ACTIONS || view->slot!=s->vmu_copy_slot) return;
    s->vmu.status=view->status;
    s->vmu.status.message[sizeof(s->vmu.status.message)-1]=0;
    s->confirm_vmu_copy=view->copy_ready && s->vmu_action_selected==1 && view->count &&
        s->vmu_selected<s->vmu.count && memchr(view->entries[0].name,0,sizeof(view->entries[0].name));
    if(s->confirm_vmu_copy) s->vmu.entries[s->vmu_selected]=view->entries[0];
    else if(view->status.complete) s->vmu.count=0;
}
void kui_shell_set_clock(struct kui_shell *s,const struct kui_datetime *value,const char *notice) {
    if(!s) return;
    bool read_valid=value && kui_datetime_valid(value);
    if(read_valid) s->clock_draft=*value;
    else if(!kui_datetime_valid(&s->clock_draft))
        s->clock_draft=(struct kui_datetime){1980,1,1,0,0,0};
    /* A dead/reset RTC must still be repairable. The explicit read-error
     * notice distinguishes this editable fallback from an observed time. */
    s->clock_valid=true;
    s->confirm_clock=false;
    snprintf(s->clock_notice,sizeof(s->clock_notice),"%s",notice?notice:
        read_valid?"":"Clock unavailable. Edit the fallback date before applying.");
}
static enum kui_shell_action list_backups(struct kui_shell *s,bool first) {
    if(first) s->backup_page=0;
    s->backup_selected=0;s->restore_path[0]=0;s->confirm_vmu_restore=false;
    memset(&s->backups,0,sizeof(s->backups));
    return KUI_SHELL_VMU_BACKUPS_LIST;
}
void kui_shell_set_cd_audio(struct kui_shell *s,const struct kui_cd_audio_status *status) {
    if(!s || !status) return;
    s->cd_audio=*status;
    if(s->cd_audio.count>99) s->cd_audio.count=99;
    s->cd_audio.message[sizeof(s->cd_audio.message)-1]=0;
    if(s->cd_selected>=s->cd_audio.count) s->cd_selected=0;
}
void kui_shell_set_music_listing(struct kui_shell *s,const struct kui_music_player_page *page) {
    if(!s || !page || !memchr(page->root,0,sizeof(page->root)) ||
       strcmp(page->root,s->music_path)) return;
    s->music_listing=*page;
    if(s->music_listing.count>KUI_MUSIC_PLAYER_ROWS) s->music_listing.count=KUI_MUSIC_PLAYER_ROWS;
    s->music_listing.message[sizeof(s->music_listing.message)-1]=0;
    for(unsigned i=0;i<s->music_listing.count;i++) {
        struct kui_music_player_entry *entry=&s->music_listing.entries[i];
        if(!memchr(entry->name,0,sizeof(entry->name))) {
            snprintf(entry->name,sizeof(entry->name),"[Name too long]");
            entry->disabled=true;
        }
    }
    if(s->music_selected>=s->music_listing.count) s->music_selected=0;
}
static enum kui_shell_action list_music(struct kui_shell *s,bool first) {
    if(first) s->music_page=0;
    s->music_selected=0;
    memset(&s->music_listing,0,sizeof(s->music_listing));
    return KUI_SHELL_MUSIC_LIST;
}
/* Entry paths are worker-owned card-root paths. Reject unsafe or truncated
 * publications before copying one into a request; the image reader validates
 * the actual GDI and its filenames independently. */
static bool games_path_safe(const char *path,size_t capacity) {
    if(!path || !memchr(path,0,capacity) || path[0]!='/' || !path[1]) return false;
    const char *component=path+1;
    for(const char *at=component;;at++) {
        unsigned char c=(unsigned char)*at;
        if(c && (c<32 || c==127 || c=='\\' || c==':')) return false;
        if(!c || c=='/') {
            size_t n=(size_t)(at-component);
            if(!n || (n==1 && component[0]=='.') ||
               (n==2 && component[0]=='.' && component[1]=='.')) return false;
            if(!c) return true;
            component=at+1;
        }
    }
}
static bool games_path_in_root(const struct kui_shell *s,const char *path,size_t capacity) {
    size_t root_length=strlen(s->games_path);
    return games_path_safe(path,capacity) && (!strcmp(s->games_path,"/") ||
        (!strncmp(path,s->games_path,root_length) && path[root_length]=='/'));
}
static void clear_game_detail(struct kui_shell *s) {
    s->games_selected_path[0]=0;
    s->games_retail_scrambled=false;
    memset(&s->games_detail,0,sizeof(s->games_detail));
}
static void clear_game_choice(struct kui_shell *s) {
    clear_game_detail(s);
    s->games_original_path[0]=s->games_2048_path[0]=0;
    s->games_variant_selected=0;
}
static bool games_pair_ready(const struct kui_shell *s) {
    return s && s->games_variant_selected<2 &&
        games_path_in_root(s,s->games_original_path,sizeof(s->games_original_path)) &&
        games_path_in_root(s,s->games_2048_path,sizeof(s->games_2048_path)) &&
        strcmp(s->games_original_path,s->games_2048_path);
}
static const char *games_variant_path(const struct kui_shell *s) {
    return s->games_variant_selected?s->games_2048_path:s->games_original_path;
}
const char *kui_shell_games_variant_label(const struct kui_shell *s) {
    if(!games_pair_ready(s) || (s->page!=KUI_SHELL_GAMES_VARIANTS &&
       (!games_path_safe(s->games_selected_path,sizeof(s->games_selected_path)) ||
        strcmp(s->games_selected_path,games_variant_path(s))))) return NULL;
    return s->games_variant_selected?"2048-byte copy":"Original";
}
void kui_shell_set_games_listing(struct kui_shell *s,const struct kui_games_page *page) {
    if(!s || !page || s->page!=KUI_SHELL_GAMES ||
       !memchr(page->root,0,sizeof(page->root)) || strcmp(page->root,s->games_path)) return;
    clear_game_choice(s);
    s->games_listing=*page;
    s->games_loading=false;s->games_art_loading=false;
    s->games_scanning=false;
    if(page->view<KUI_GAMES_VIEW_COUNT) s->games_view=page->view;
    if(s->games_listing.count>KUI_GAMES_ROWS) s->games_listing.count=KUI_GAMES_ROWS;
    s->games_listing.message[sizeof(s->games_listing.message)-1]=0;
    for(unsigned i=0;i<s->games_listing.count;i++) {
        struct kui_games_entry *e=&s->games_listing.entries[i];
        e->title[sizeof(e->title)-1]=0;
        if(!memchr(e->name,0,sizeof(e->name))) {
            snprintf(e->name,sizeof(e->name),"[Name too long]");e->disabled=true;e->title[0]=0;
        }
        if(!games_path_in_root(s,e->path,sizeof(e->path))) {
            e->path[0]=0;e->disabled=true;
        }
        /* An invalid alternate cannot turn a valid Original into a pair.
         * The original remains accessible through the normal single flow. */
        if(e->disabled || e->directory ||
           !games_path_in_root(s,e->variant_2048_path,sizeof(e->variant_2048_path)) ||
           !strcmp(e->path,e->variant_2048_path)) e->variant_2048_path[0]=0;
        if(e->directory) {
            char normalized[KUI_DEST_ROOT_CAP];
            if(!kui_destination_normalize(normalized,e->path) || strcmp(normalized,e->path))
                e->disabled=true;
        }
    }
    for(unsigned i=0;i<s->games_listing.count;i++)
        if(s->games_listing.entries[i].disabled) s->games_listing.entries[i].cover=false;
    if(s->games_selected>=s->games_listing.count) s->games_selected=0;
}
unsigned kui_shell_games_view(const struct kui_shell *s) {
    return s && s->games_view<KUI_GAMES_VIEW_COUNT?s->games_view:KUI_GAMES_VIEW_LIST;
}
bool kui_shell_set_games_rows(struct kui_shell *s,const struct kui_games_page *page,
    unsigned generation,unsigned offset,unsigned requested_view) {
    if(!s || !page || s->page!=KUI_SHELL_GAMES || s->games_generation!=generation ||
       s->games_page>UINT_MAX/KUI_GAMES_ROWS || s->games_page*KUI_GAMES_ROWS!=offset ||
       s->games_view!=requested_view || !memchr(page->root,0,sizeof(page->root)) ||
       strcmp(page->root,s->games_path)) return false;
    kui_shell_set_games_listing(s,page);
    return true;
}
bool kui_shell_games_art_key(const struct kui_shell *s,struct kui_shell_games_art_key *out) {
    if(!s || !out || s->page!=KUI_SHELL_GAMES || s->games_loading ||
       s->games_selected>=s->games_listing.count ||
       s->games_listing.view!=kui_shell_games_view(s) ||
       strcmp(s->games_listing.root,s->games_path)) return false;
    const struct kui_games_entry *e=&s->games_listing.entries[s->games_selected];
    if(e->directory || e->disabled || !games_path_in_root(s,e->path,sizeof(e->path))) return false;
    *out=(struct kui_shell_games_art_key){.generation=s->games_generation,
        .page=s->games_page,.view=kui_shell_games_view(s),.row=s->games_selected};
    memcpy(out->root,s->games_path,sizeof(out->root));
    memcpy(out->path,e->path,sizeof(out->path));
    return true;
}
bool kui_shell_games_art_same(const struct kui_shell_games_art_key *a,const struct kui_shell_games_art_key *b) {
    return a && b && a->generation==b->generation && a->page==b->page && a->view==b->view && a->row==b->row &&
        memchr(a->root,0,sizeof(a->root)) && memchr(b->root,0,sizeof(b->root)) &&
        memchr(a->path,0,sizeof(a->path)) && memchr(b->path,0,sizeof(b->path)) &&
        !strcmp(a->root,b->root) && !strcmp(a->path,b->path);
}
bool kui_shell_set_games_art(struct kui_shell *s,const struct kui_shell_games_art_key *key,
    const struct kui_games_cover_result *result) {
    struct kui_shell_games_art_key current;
    if(!result || result->stopped || !kui_shell_games_art_key(s,&current) ||
       !kui_shell_games_art_same(key,&current) || result->size!=(current.view==KUI_GAMES_VIEW_LIST?
           KUI_COVER_SIZE_LARGE:current.view==KUI_GAMES_VIEW_COMPACT?KUI_COVER_SIZE_SMALL:KUI_COVER_SIZE_MEDIUM) ||
       !memchr(result->path,0,sizeof(result->path)) || strcmp(result->path,current.path) ||
       !memchr(result->name,0,sizeof(result->name)) ||
       strcmp(result->name,s->games_listing.entries[current.row].name) ||
       !memchr(result->title,0,sizeof(result->title))) return false;
    for(unsigned i=0;i<s->games_listing.count;i++) s->games_listing.entries[i].cover=false;
    struct kui_games_entry *e=&s->games_listing.entries[current.row];
    e->cover=result->cover;
    if(result->title[0]) memcpy(e->title,result->title,sizeof(e->title));
    if(result->cover) s->games_listing.artwork=true;
    s->games_art_loading=false;
    return true;
}
void kui_shell_set_games_detail(struct kui_shell *s,const struct kui_games_detail *detail) {
    if(!s || !detail || s->page!=KUI_SHELL_GAMES_DETAIL ||
       !memchr(detail->path,0,sizeof(detail->path)) || strcmp(detail->path,s->games_selected_path)) return;
    s->games_detail=*detail;
    s->games_retail_scrambled=false;
    s->games_detail.title[sizeof(s->games_detail.title)-1]=0;
    s->games_detail.product[sizeof(s->games_detail.product)-1]=0;
    s->games_detail.region[sizeof(s->games_detail.region)-1]=0;
    s->games_detail.boot_file[sizeof(s->games_detail.boot_file)-1]=0;
    s->games_detail.message[sizeof(s->games_detail.message)-1]=0;
}
bool kui_shell_games_image_ready(const struct kui_shell *s) {
    return s && s->games_detail.valid &&
        games_path_safe(s->games_selected_path,sizeof(s->games_selected_path)) &&
        (!(s->games_original_path[0] || s->games_2048_path[0]) ||
         (games_pair_ready(s) && !strcmp(s->games_selected_path,games_variant_path(s)))) &&
        memchr(s->games_detail.path,0,sizeof(s->games_detail.path)) &&
        !strcmp(s->games_detail.path,s->games_selected_path);
}
bool kui_shell_games_retail_ready(const struct kui_shell *s) {
    return kui_shell_games_image_ready(s) &&
        memchr(s->games_detail.title,0,sizeof(s->games_detail.title)) &&
        memchr(s->games_detail.boot_file,0,sizeof(s->games_detail.boot_file)) &&
        (s->games_detail.native_gd || s->games_detail.native_cd) && !s->games_detail.windows_ce &&
        s->games_detail.boot_file[0] &&
        s->games_detail.tracks && s->games_detail.tracks<=KUI_RETAIL_IMAGE_TRACKS &&
        (s->games_detail.format!=KUI_GAME_IMAGE_GDI || s->games_detail.boot_lba>=45000) && s->games_detail.boot_bytes>=128 &&
        s->games_detail.boot_bytes<=KUI_RETAIL_IMAGE_BOOT_MAX;
}
bool kui_shell_games_ce_probe_ready(const struct kui_shell *s) {
    /* The boot file holds a 2048-byte load prefix, then the kernel body. */
    return kui_shell_games_image_ready(s) &&
        memchr(s->games_detail.title,0,sizeof(s->games_detail.title)) &&
        memchr(s->games_detail.boot_file,0,sizeof(s->games_detail.boot_file)) &&
        s->games_detail.windows_ce && !s->games_detail.native_gd && !s->games_detail.native_cd &&
        s->games_detail.boot_file[0] &&
        s->games_detail.tracks && s->games_detail.tracks<=KUI_RETAIL_IMAGE_TRACKS &&
        (s->games_detail.format!=KUI_GAME_IMAGE_GDI || s->games_detail.boot_lba>=45000) && s->games_detail.boot_bytes>2048 &&
        s->games_detail.boot_bytes<=KUI_RETAIL_IMAGE_BOOT_MAX;
}
bool kui_shell_games_encoding_ready(const struct kui_shell *s) {
    return kui_shell_games_retail_ready(s) && s->games_detail.cd_image;
}
static enum kui_shell_action list_games(struct kui_shell *s,bool first) {
    clear_game_choice(s);
    s->games_refresh=false;
    ++s->games_generation;s->games_loading=true;s->games_art_loading=false;
    if(first) s->games_page=0;
    s->games_selected=0;
    snprintf(s->games_listing.message,sizeof(s->games_listing.message),"Reading SD directory...");
    return KUI_SHELL_GAMES_LIST;
}
static unsigned move_count(unsigned selected, unsigned buttons,unsigned count);
/* Turning a page from a grid edge lands on the matching cell; the listing
 * clamps it if the new page is shorter. */
static enum kui_shell_action turn_games_page(struct kui_shell *s,bool forward,unsigned select) {
    if(forward) {
        if(!s->games_listing.has_more || s->games_page>=UINT_MAX/KUI_GAMES_ROWS) return KUI_SHELL_NONE;
        ++s->games_page;
    } else {
        if(!s->games_page) return KUI_SHELL_NONE;
        --s->games_page;
    }
    enum kui_shell_action action=list_games(s,false);
    s->games_selected=select;
    return action;
}
/* Compact: two columns of four, filled down the first column. Gallery: two
 * rows of four, filled across. Moving past a side edge turns the page. */
static bool games_grid(struct kui_shell *s,unsigned buttons,enum kui_shell_action *action) {
    unsigned view=kui_shell_games_view(s),count=s->games_listing.count,at=s->games_selected;
    unsigned horizontal=buttons&(KUI_SHELL_LEFT|KUI_SHELL_RIGHT),vertical=buttons&(KUI_SHELL_UP|KUI_SHELL_DOWN);
    *action=KUI_SHELL_NONE;
    if(view==KUI_GAMES_VIEW_LIST) return false;
    if(at>=count) at=0;
    if(view==KUI_GAMES_VIEW_COMPACT) {
        unsigned column=at/4u,row=at%4u;
        if(horizontal==KUI_SHELL_LEFT) {
            if(column) s->games_selected=at-4u; else *action=turn_games_page(s,false,row+4u);
        } else if(horizontal==KUI_SHELL_RIGHT) {
            if(!column && at+4u<count) s->games_selected=at+4u; else *action=turn_games_page(s,true,row);
        } else s->games_selected=move_count(at,buttons,count);
        return true;
    }
    unsigned row=at/4u,column=at%4u;
    if(horizontal==KUI_SHELL_LEFT) {
        if(column) s->games_selected=at-1u; else *action=turn_games_page(s,false,row*4u+3u);
    } else if(horizontal==KUI_SHELL_RIGHT) {
        if(column<3u && at+1u<count) s->games_selected=at+1u; else *action=turn_games_page(s,true,row*4u);
    } else if(vertical==KUI_SHELL_UP || vertical==KUI_SHELL_DOWN) {
        if(row) s->games_selected=at-4u; else if(at+4u<count) s->games_selected=at+4u;
    }
    return true;
}
static enum kui_shell_action inspect_game(struct kui_shell *s) {
    ++s->games_generation;s->games_art_loading=false;
    s->games_retail_scrambled=false;
    memset(&s->games_detail,0,sizeof(s->games_detail));
    snprintf(s->games_detail.path,sizeof(s->games_detail.path),"%s",s->games_selected_path);
    snprintf(s->games_detail.message,sizeof(s->games_detail.message),"Inspecting image metadata...");
    s->page=KUI_SHELL_GAMES_DETAIL;
    return KUI_SHELL_GAMES_INSPECT;
}
unsigned kui_shell_progress_tenths(uint64_t done,uint64_t total) {
    if(!total) return 0;
    if(done>=total) return 1000;
    /* Multiplication is exact in the common case and bounded for malformed
     * snapshots. Division first preserves a floor, never 100% before done. */
    if(done<=UINT64_MAX/1000u) return (unsigned)(done*1000u/total);
    return (unsigned)((double)done/(double)total*1000.0) > 999u ? 999u :
        (unsigned)((double)done/(double)total*1000.0);
}
bool kui_shell_phase_eta(const struct kui_shell_view *v,uint64_t *seconds) {
    if(!v || !seconds || !v->busy || v->saving || v->cancel_requested ||
       v->phase<1 || v->phase>4 || !v->total || !v->rate_kib ||
       v->phase_elapsed_ms<2000 || v->progress_age_ms>3000) return false;
    uint64_t bytes_per_second=(uint64_t)v->rate_kib*1024u;
    uint64_t remaining=v->done<v->total?v->total-v->done:0;
    *seconds=remaining/bytes_per_second+(remaining%bytes_per_second!=0);
    return true;
}
void kui_shell_destination_error(struct kui_shell *s, const char *message) {
    if(s) snprintf(s->destination_notice,sizeof(s->destination_notice),"%s",
        message ? message : "Could not open this folder.");
}
void kui_shell_set_destination(struct kui_shell *s, const char *path) {
    char normalized[KUI_DEST_ROOT_CAP];
    if(!s || !kui_destination_normalize(normalized,path)) return;
    snprintf(s->destination,sizeof(s->destination),"%s",normalized);
    snprintf(s->browse_path,sizeof(s->browse_path),"%s",normalized);
    s->destination_notice[0]=0;
    if(s->page==KUI_SHELL_DESTINATION || s->page==KUI_SHELL_KEYBOARD)
        s->page=KUI_SHELL_RIPPER;
}
void kui_shell_set_listing(struct kui_shell *s, const struct kui_destination_page *page) {
    if(!s || !page) return;
    s->listing=*page;
    if(s->listing.count>KUI_DEST_PAGE_SIZE) s->listing.count=KUI_DEST_PAGE_SIZE;
    for(unsigned i=0;i<s->listing.count;i++) {
        struct kui_destination_entry *entry=&s->listing.entries[i];
        if(!memchr(entry->name,0,sizeof(entry->name))) {
            snprintf(entry->name,sizeof(entry->name),"[Name too long]");
            entry->disabled=true;
        }
    }
    s->browser_selected=0;
    s->destination_notice[0]=0;
}
static enum kui_shell_action list_destination(struct kui_shell *s, bool first_page) {
    if(first_page) s->browser_page=0;
    s->browser_selected=0;
    memset(&s->listing,0,sizeof(s->listing));
    s->destination_notice[0]=0;
    return KUI_SHELL_DEST_LIST;
}
static enum kui_shell_action save_destination(struct kui_shell *s, const char *path) {
    char normalized[KUI_DEST_ROOT_CAP];
    if(!kui_destination_normalize(normalized,path)) {
        kui_shell_destination_error(s,"Use an absolute folder path without '..' or reserved names.");
        return KUI_SHELL_NONE;
    }
    snprintf(s->browse_path,sizeof(s->browse_path),"%s",normalized);
    s->destination_notice[0]=0;
    return KUI_SHELL_DEST_SAVE;
}
/* ---- File Manager ---- */
#define FILES_ACTION_COUNT 7u
static const struct kui_files_entry *files_entry(const struct kui_shell *s) {
    return s->files_selected<s->files_listing.count?&s->files_listing.entries[s->files_selected]:NULL;
}
/* The selected row's card path, unless the row cannot be used. */
static bool files_entry_path(const struct kui_shell *s,char out[KUI_FILES_PATH_CAP]) {
    const struct kui_files_entry *e=files_entry(s);
    return e && !e->disabled && kui_files_join(out,s->files_path,e->name);
}
static void files_say(struct kui_shell *s,bool error,const char *text) {
    snprintf(s->files_notice,sizeof(s->files_notice),"%s",text);
    s->files_notice_detail[0]=0;s->files_notice_error=error;
}
static void files_quiet(struct kui_shell *s) {s->files_notice[0]=s->files_notice_detail[0]=0;s->files_notice_error=false;}
/* Asks for a page of the browser's folder, or the picker's. The anchor is
 * copied before the page it may belong to is cleared. */
static enum kui_shell_action list_files(struct kui_shell *s,bool picker,enum kui_files_seek seek,
        const char *anchor,bool anchor_directory) {
    struct kui_files_request *r=&s->files_request;
    memset(r,0,sizeof(*r));
    memcpy(r->path,picker?s->files_pick_path:s->files_path,sizeof(r->path));
    r->path[sizeof(r->path)-1]=0;
    r->folders_only=picker;
    r->seek=KUI_FILES_SEEK_FIRST;
    if(seek!=KUI_FILES_SEEK_FIRST && anchor && memchr(anchor,0,KUI_FILES_KEY_CAP) && anchor[0]) {
        memcpy(r->anchor,anchor,strlen(anchor)+1);
        r->anchor_directory=anchor_directory;r->seek=seek;
    }
    struct kui_files_page *page=picker?&s->files_pick:&s->files_listing;
    memset(page,0,sizeof(*page));
    memcpy(page->path,r->path,sizeof(page->path));
    page->folders_only=picker;
    snprintf(page->message,sizeof(page->message),"Reading folder...");
    if(picker) s->files_pick_selected=0; else s->files_selected=0;
    return KUI_SHELL_FILES_LIST;
}
static enum kui_shell_action files_page_turn(struct kui_shell *s,bool picker,bool forward) {
    const struct kui_files_page *l=picker?&s->files_pick:&s->files_listing;
    if(forward) {
        if(!l->count || l->before+l->count>=l->total) return KUI_SHELL_NONE;
        return list_files(s,picker,KUI_FILES_SEEK_NEXT,l->last,l->last_directory);
    }
    if(!l->before) return KUI_SHELL_NONE;
    if(l->before<=KUI_FILES_ROWS || !l->count) return list_files(s,picker,KUI_FILES_SEEK_FIRST,NULL,false);
    return list_files(s,picker,KUI_FILES_SEEK_PREVIOUS,l->first,l->first_directory);
}
/* Lists the browser's folder again from its current first row. */
static enum kui_shell_action files_refresh(struct kui_shell *s) {
    const struct kui_files_page *l=&s->files_listing;
    return l->count?list_files(s,false,KUI_FILES_SEEK_AT,l->first,l->first_directory):
        list_files(s,false,KUI_FILES_SEEK_FIRST,NULL,false);
}
static void files_begin(struct kui_shell *s,enum kui_files_op op,const char *source) {
    memset(&s->files_job,0,sizeof(s->files_job));
    s->files_job.op=op;
    memcpy(s->files_job.source,source,strlen(source)+1);
}
/* Checks the job on its own page: details, or a confirmation that shows
 * what the check found. */
static enum kui_shell_action files_check(struct kui_shell *s) {
    memset(&s->files_preview,0,sizeof(s->files_preview));
    snprintf(s->files_preview.status.message,sizeof(s->files_preview.status.message),"Checking...");
    s->files_job.name[0]=0;
    s->page=s->files_job.op==KUI_FILES_OP_DETAILS?KUI_SHELL_FILES_INFO:KUI_SHELL_FILES_CONFIRM;
    return KUI_SHELL_FILES_CHECK;
}
static enum kui_shell_action files_keyboard(struct kui_shell *s,enum kui_files_op op) {
    char path[KUI_FILES_PATH_CAP];
    if(op==KUI_FILES_OP_RENAME) {
        const struct kui_files_entry *e=files_entry(s);
        if(!e || !files_entry_path(s,path)) return KUI_SHELL_NONE;
        files_begin(s,op,path);
        memcpy(s->keyboard,e->name,strlen(e->name)+1);
    } else {
        files_begin(s,op,s->files_path);
        s->keyboard[0]=0;
    }
    memcpy(s->keyboard_original,s->keyboard,sizeof(s->keyboard_original));
    s->keyboard_selected=0;s->keyboard_layer=KUI_SHELL_KEYS_LOWER;s->destination_notice[0]=0;
    s->files_keyboard=true;s->page=KUI_SHELL_KEYBOARD;
    return KUI_SHELL_NONE;
}
static enum kui_shell_action files_name_done(struct kui_shell *s) {
    if(!s->keyboard[0]) {kui_shell_destination_error(s,"Type a name first.");return KUI_SHELL_NONE;}
    if(!kui_destination_name_valid(s->keyboard)) {
        kui_shell_destination_error(s,"Use a name without / that does not end in a space or dot.");
        return KUI_SHELL_NONE;
    }
    memcpy(s->files_job.name,s->keyboard,strlen(s->keyboard)+1);
    const struct kui_files_entry *e=files_entry(s);
    bool directory=s->files_job.op==KUI_FILES_OP_MKDIR || (e && e->directory);
    bool rename=s->files_job.op==KUI_FILES_OP_RENAME;
    s->files_keyboard=false;s->page=KUI_SHELL_FILES;
    /* The folder is listed again from the new name, which is selected. */
    list_files(s,false,KUI_FILES_SEEK_AT,s->files_job.name,directory);
    files_say(s,false,rename?"Renaming...":"Creating folder...");
    s->files_running=true;
    return KUI_SHELL_FILES_RUN;
}
static enum kui_shell_action files_open(struct kui_shell *s) {
    const struct kui_files_entry *e=files_entry(s);
    char path[KUI_FILES_PATH_CAP];
    if(!e) return KUI_SHELL_NONE;
    if(!files_entry_path(s,path)) {
        s->page=KUI_SHELL_FILES;
        files_say(s,true,"K-UI cannot use this name; rename it on a computer.");
        return KUI_SHELL_NONE;
    }
    switch(kui_files_kind(e->name,e->directory)) {
    case KUI_FILES_KIND_FOLDER:
        s->page=KUI_SHELL_FILES;files_quiet(s);
        memcpy(s->files_path,path,sizeof(s->files_path));
        return list_files(s,false,KUI_FILES_SEEK_FIRST,NULL,false);
    case KUI_FILES_KIND_GDI:
        clear_game_choice(s);
        memcpy(s->games_selected_path,path,sizeof(s->games_selected_path));
        s->games_from_files=true;
        return inspect_game(s);
    case KUI_FILES_KIND_AUDIO:
        s->page=KUI_SHELL_FILES;
        if(strlen(path)>=sizeof(s->music_selected_path)) {
            files_say(s,true,"This path is too long for the music player.");
            return KUI_SHELL_NONE;
        }
        memcpy(s->music_selected_path,path,strlen(path)+1);
        files_say(s,false,"Loading music...");
        return KUI_SHELL_MUSIC_PLAY;
    case KUI_FILES_KIND_PICTURE:
        memset(&s->files_picture,0,sizeof(s->files_picture));
        memcpy(s->files_picture.path,path,sizeof(s->files_picture.path));
        s->files_picture.format="";
        snprintf(s->files_picture.message,sizeof(s->files_picture.message),"Loading picture...");
        s->page=KUI_SHELL_FILES_VIEW;
        return KUI_SHELL_FILES_PICTURE;
    default:
        files_begin(s,KUI_FILES_OP_DETAILS,path);
        return files_check(s);
    }
}
/* Actions menu: Open, Copy, Move, Rename, Delete, Details, New folder. */
static enum kui_shell_action files_action(struct kui_shell *s) {
    unsigned item=s->files_action_selected;
    if(item==6) return files_keyboard(s,KUI_FILES_OP_MKDIR);
    char path[KUI_FILES_PATH_CAP];
    if(!files_entry_path(s,path)) {
        files_say(s,true,"K-UI cannot use this name; rename it on a computer.");
        return KUI_SHELL_NONE;
    }
    if((item==2 || item==3 || item==4) && kui_files_protected(path)) {
        files_say(s,true,"K-UI needs this to start; it cannot be moved, renamed or deleted.");
        return KUI_SHELL_NONE;
    }
    files_quiet(s);
    switch(item) {
    case 0: return files_open(s);
    case 1: case 2:
        files_begin(s,item==1?KUI_FILES_OP_COPY:KUI_FILES_OP_MOVE,path);
        memcpy(s->files_pick_path,s->files_path,sizeof(s->files_pick_path));
        s->page=KUI_SHELL_FILES_PICK;
        return list_files(s,true,KUI_FILES_SEEK_FIRST,NULL,false);
    case 3: return files_keyboard(s,KUI_FILES_OP_RENAME);
    case 4: files_begin(s,KUI_FILES_OP_DELETE,path); return files_check(s);
    default: files_begin(s,KUI_FILES_OP_DETAILS,path); return files_check(s);
    }
}
static enum kui_shell_action files_input(struct kui_shell *s,unsigned buttons) {
    const struct kui_files_page *l=&s->files_listing;
    unsigned horizontal=buttons&(KUI_SHELL_LEFT|KUI_SHELL_RIGHT);
    if(buttons&KUI_SHELL_START) {s->page=KUI_SHELL_HOME;return KUI_SHELL_NONE;}
    if(buttons&KUI_SHELL_R) {files_quiet(s);return files_refresh(s);}
    if(buttons&KUI_SHELL_Y) return files_keyboard(s,KUI_FILES_OP_MKDIR);
    if(horizontal==KUI_SHELL_LEFT || horizontal==KUI_SHELL_RIGHT)
        return files_page_turn(s,false,horizontal==KUI_SHELL_RIGHT);
    unsigned before=s->files_selected;
    s->files_selected=move_count(s->files_selected,buttons,l->count);
    if(s->files_selected!=before) s->files_notice_detail[0]=0;
    if((buttons&KUI_SHELL_X) && s->files_selected<l->count) {
        s->files_action_selected=0;files_quiet(s);s->page=KUI_SHELL_FILES_ACTIONS;
        return KUI_SHELL_NONE;
    }
    if(buttons&KUI_SHELL_A) return files_open(s);
    return KUI_SHELL_NONE;
}
static enum kui_shell_action files_pick_input(struct kui_shell *s,unsigned buttons) {
    const struct kui_files_page *l=&s->files_pick;
    unsigned horizontal=buttons&(KUI_SHELL_LEFT|KUI_SHELL_RIGHT);
    if(buttons&KUI_SHELL_START) {s->page=KUI_SHELL_FILES;return KUI_SHELL_NONE;}
    if(buttons&KUI_SHELL_Y) {
        memcpy(s->files_job.target,s->files_pick_path,sizeof(s->files_job.target));
        return files_check(s);
    }
    if(horizontal==KUI_SHELL_LEFT || horizontal==KUI_SHELL_RIGHT)
        return files_page_turn(s,true,horizontal==KUI_SHELL_RIGHT);
    s->files_pick_selected=move_count(s->files_pick_selected,buttons,l->count);
    if((buttons&KUI_SHELL_A) && s->files_pick_selected<l->count) {
        const struct kui_files_entry *e=&l->entries[s->files_pick_selected];
        char child[KUI_FILES_PATH_CAP];
        if(e->disabled || !kui_files_join(child,s->files_pick_path,e->name)) {
            snprintf(s->files_pick.message,sizeof(s->files_pick.message),"%s",
                kui_files_join(child,s->files_pick_path,e->name) && !strcmp(child,s->files_job.source)?
                "This is the folder being copied or moved.":"This folder cannot be opened.");
            return KUI_SHELL_NONE;
        }
        memcpy(s->files_pick_path,child,sizeof(s->files_pick_path));
        return list_files(s,true,KUI_FILES_SEEK_FIRST,NULL,false);
    }
    return KUI_SHELL_NONE;
}
bool kui_shell_files_ready(const struct kui_shell *s) {
    if(!s) return false;
    const struct kui_files_preview *p=&s->files_preview;
    enum kui_files_op op=s->files_job.op;
    bool moving=op==KUI_FILES_OP_COPY || op==KUI_FILES_OP_MOVE;
    return (moving || op==KUI_FILES_OP_DELETE) && p->ready && p->status.passed && p->job.op==op &&
        memchr(p->job.source,0,sizeof(p->job.source)) && !strcmp(p->job.source,s->files_job.source) &&
        kui_files_path_valid(s->files_job.source) &&
        (!moving || (memchr(p->job.target,0,sizeof(p->job.target)) && !strcmp(p->job.target,s->files_job.target) &&
                     memchr(s->files_job.name,0,sizeof(s->files_job.name)) &&
                     kui_destination_name_valid(s->files_job.name)));
}
void kui_shell_set_files_listing(struct kui_shell *s,const struct kui_files_page *page) {
    if(!s || !page || !memchr(page->path,0,sizeof(page->path))) return;
    bool picker=page->folders_only;
    if(picker?(s->page!=KUI_SHELL_FILES_PICK || strcmp(page->path,s->files_pick_path)):
              strcmp(page->path,s->files_path)) return;
    struct kui_files_page *l=picker?&s->files_pick:&s->files_listing;
    *l=*page;
    l->message[sizeof(l->message)-1]=0;
    if(l->count>KUI_FILES_ROWS) l->count=KUI_FILES_ROWS;
    if(l->before>l->total) l->before=l->total;
    if(!l->count || !memchr(l->first,0,sizeof(l->first)) || !memchr(l->last,0,sizeof(l->last))) {
        l->first[0]=l->last[0]=0;
        if(l->count) l->count=0;
    }
    bool moving=s->files_job.op==KUI_FILES_OP_COPY || s->files_job.op==KUI_FILES_OP_MOVE;
    for(unsigned i=0;i<l->count;i++) {
        struct kui_files_entry *e=&l->entries[i];
        char path[KUI_FILES_PATH_CAP];
        if(!memchr(e->name,0,sizeof(e->name))) {
            snprintf(e->name,sizeof(e->name),"[Name too long]");e->disabled=true;
        }
        if(!e->disabled && !kui_files_join(path,l->path,e->name)) e->disabled=true;
        /* A copied or moved folder cannot be chosen as its own destination. */
        if(picker && moving && !e->disabled && !strcmp(path,s->files_job.source)) e->disabled=true;
    }
    unsigned *selected=picker?&s->files_pick_selected:&s->files_selected;
    if(*selected>=l->count) *selected=0;
}
void kui_shell_set_files_preview(struct kui_shell *s,const struct kui_files_preview *preview) {
    if(!s || !preview) return;
    enum kui_files_op op=s->files_job.op;
    bool moving=op==KUI_FILES_OP_COPY || op==KUI_FILES_OP_MOVE;
    if(preview->job.op!=op || s->page!=(op==KUI_FILES_OP_DETAILS?KUI_SHELL_FILES_INFO:KUI_SHELL_FILES_CONFIRM) ||
       !memchr(preview->job.source,0,sizeof(preview->job.source)) || strcmp(preview->job.source,s->files_job.source) ||
       (moving && (!memchr(preview->job.target,0,sizeof(preview->job.target)) ||
                   strcmp(preview->job.target,s->files_job.target)))) return;
    s->files_preview=*preview;
    struct kui_app_status *st=&s->files_preview.status;
    st->message[sizeof(st->message)-1]=0;
    if(st->line_count>KUI_APP_LINES) st->line_count=KUI_APP_LINES;
    for(unsigned i=0;i<st->line_count;i++) st->lines[i][KUI_APP_LINE_CAP-1]=0;
    s->files_preview.job.name[sizeof(s->files_preview.job.name)-1]=0;
    if(moving) {
        const char *name=s->files_preview.job.name;
        if(s->files_preview.ready && kui_destination_name_valid(name)) memcpy(s->files_job.name,name,strlen(name)+1);
        else s->files_preview.ready=false;
    }
}
void kui_shell_set_files_status(struct kui_shell *s,const struct kui_app_status *status) {
    if(!s || !status) return;
    char message[sizeof(status->message)];
    memcpy(message,status->message,sizeof(message));message[sizeof(message)-1]=0;
    files_say(s,!status->passed && !status->stopped,message);
    s->files_running=false;
    if(status->line_count && status->line_count<=KUI_APP_LINES) {
        memcpy(s->files_notice_detail,status->lines[0],sizeof(s->files_notice_detail));
        s->files_notice_detail[sizeof(s->files_notice_detail)-1]=0;
    }
}
void kui_shell_set_files_picture(struct kui_shell *s,const struct kui_files_picture *picture) {
    if(!s || !picture || s->page!=KUI_SHELL_FILES_VIEW || !memchr(picture->path,0,sizeof(picture->path)) ||
       strcmp(picture->path,s->files_picture.path)) return;
    s->files_picture=*picture;
    s->files_picture.message[sizeof(s->files_picture.message)-1]=0;
    if(!s->files_picture.format) s->files_picture.format="";
}
static const char keyboard_keys[]="qwertyuiopasdfghjkl/zxcvbnm-_.0123456789";
void kui_shell_set_storage_test_result(struct kui_shell *s,const struct kui_storage_test_result *result) {
    if(!s || !result) return;
    s->storage_test_result=*result;
    s->storage_test_result.sample_count=result->sample_count>KUI_STORAGE_TEST_SAMPLES?
        KUI_STORAGE_TEST_SAMPLES:result->sample_count;
    s->storage_test_result.message[sizeof(result->message)-1]=0;
    s->storage_test_result.path[sizeof(result->path)-1]=0;
    s->storage_test_last_request=result->request;
    s->storage_test_last_valid=kui_storage_test_request_valid(&result->request);
    s->storage_test_show_result=true;s->storage_test_from_history=false;
    s->storage_test_details=false;s->storage_test_chunk=1;
}
void kui_shell_set_storage_test_history(struct kui_shell *s,const struct kui_storage_test_history *history) {
    if(!s || !history) return;
    uint32_t selected=s->storage_history_selected<s->storage_test_history.count?
        s->storage_test_history.rows[s->storage_history_selected].id:0;
    s->storage_test_history=*history;
    if(s->storage_test_history.count>KUI_STORAGE_TEST_HISTORY)
        s->storage_test_history.count=KUI_STORAGE_TEST_HISTORY;
    s->storage_test_history.message[sizeof(history->message)-1]=0;
    s->storage_history_selected=0;
    for(unsigned i=0;i<s->storage_test_history.count;i++)
        if(s->storage_test_history.rows[i].id==selected) s->storage_history_selected=i;
    if(!s->storage_test_last_valid && s->storage_test_history.count &&
       kui_storage_test_request_valid(&s->storage_test_history.rows[0].request)) {
        s->storage_test_last_request=s->storage_test_history.rows[0].request;
        s->storage_test_last_valid=true;
    }
}
/* Every other printable ASCII character, for Wi-Fi passwords above all. */
static const char symbol_keys[]="!@#$%^&*()~`=+[]{}<>\\|;:'\",.?/0123456789";
const char *kui_shell_key_label(unsigned key, unsigned layer) {
    static char character[2];
    if(key>=KUI_SHELL_KEY_COUNT) return "";
    if(key==40) return "SPACE";
    if(key==41) return "BACK";
    if(key==42) return "DONE";
    char c=layer==KUI_SHELL_KEYS_SYMBOLS?symbol_keys[key]:keyboard_keys[key];
    character[0]=layer==KUI_SHELL_KEYS_UPPER && c>='a' && c<='z' ? (char)(c-'a'+'A') : c;
    character[1]=0;
    return character;
}
static void keyboard_backspace(struct kui_shell *s) {
    size_t n=strlen(s->keyboard);
    if(!n) return;
    /* A folder already on the card may contain UTF-8 even though this small
     * keyboard enters ASCII. Backspace removes a whole encoded character. */
    --n;
    while(n && ((unsigned char)s->keyboard[n]&0xc0u)==0x80u) --n;
    s->keyboard[n]=0;
    s->destination_notice[0]=0;
}
static unsigned keyboard_move(unsigned key,unsigned buttons) {
    if(key>=KUI_SHELL_KEY_COUNT) key=0;
    unsigned row=key<40?key/10:4, col=key<40?key%10:key-40;
    unsigned horizontal=buttons&(KUI_SHELL_LEFT|KUI_SHELL_RIGHT);
    unsigned vertical=buttons&(KUI_SHELL_UP|KUI_SHELL_DOWN);
    unsigned count=row==4?3:10;
    if(horizontal==KUI_SHELL_LEFT) col=col?col-1:count-1;
    else if(horizontal==KUI_SHELL_RIGHT) col=(col+1)%count;
    if(vertical==KUI_SHELL_UP || vertical==KUI_SHELL_DOWN) {
        unsigned old_row=row;
        row=vertical==KUI_SHELL_UP?(row?row-1:4):(row+1)%5;
        if(old_row==4) col=col==0?1:col==1?4:8;
        if(row==4) col=col<3?0:col<7?1:2;
    }
    return row==4?40+col:row*10+col;
}
/* ---- Wi-Fi page ---- */
unsigned kui_shell_wifi_rows(const struct kui_shell *s) {
    return s ? 2u+(s->wifi.count<KUI_WIFI_NETWORKS?s->wifi.count:KUI_WIFI_NETWORKS) : 0;
}
void kui_shell_set_wifi(struct kui_shell *s,const struct kui_wifi_view *view) {
    if(!s || !view) return;
    struct kui_wifi_view next=*view;
    next.message[sizeof(next.message)-1]=0;next.board[sizeof(next.board)-1]=0;
    next.wifi.ssid[sizeof(next.wifi.ssid)-1]=0;
    /* A job that has only just started has not found the board yet: what
     * is shown stays until it has. */
    if(next.working && !next.found && s->wifi.found) {
        memcpy(next.board,s->wifi.board,sizeof(next.board));next.wifi=s->wifi.wifi;next.found=true;
    }
    if(!next.scanned && s->wifi.scanned && next.found) {
        memcpy(next.networks,s->wifi.networks,sizeof(next.networks));
        next.count=s->wifi.count;next.scanned=true;
    }
    if(next.count>KUI_WIFI_NETWORKS) next.count=KUI_WIFI_NETWORKS;
    for(unsigned i=0;i<next.count;i++) next.networks[i].ssid[sizeof(next.networks[i].ssid)-1]=0;
    s->wifi=next;
    if(s->wifi_selected>=kui_shell_wifi_rows(s)) s->wifi_selected=0;
}
static void wifi_keyboard(struct kui_shell *s,bool name) {
    s->keyboard[0]=s->keyboard_original[0]=0;
    s->keyboard_selected=0;s->keyboard_layer=KUI_SHELL_KEYS_LOWER;s->destination_notice[0]=0;
    s->wifi_keyboard=true;s->wifi_typing_name=name;s->page=KUI_SHELL_KEYBOARD;
}
static void wifi_keyboard_close(struct kui_shell *s) {
    memset(s->keyboard,0,sizeof(s->keyboard));
    s->wifi_keyboard=s->wifi_typing_name=false;s->destination_notice[0]=0;s->page=KUI_SHELL_WIFI;
}
static enum kui_shell_action wifi_join(struct kui_shell *s,const char *password) {
    s->wifi_request.action=KUI_WIFI_JOIN;s->wifi_request.band=KWM_BAND_KEEP;
    snprintf(s->wifi_request.password,sizeof(s->wifi_request.password),"%.64s",password);
    return KUI_SHELL_WIFI_JOIN;
}
static enum kui_shell_action wifi_name_done(struct kui_shell *s) {
    size_t n=strlen(s->keyboard);
    if(s->wifi_typing_name) {
        if(!n) {kui_shell_destination_error(s,"Type the network's name first.");return KUI_SHELL_NONE;}
        snprintf(s->wifi_request.ssid,sizeof(s->wifi_request.ssid),"%.32s",s->keyboard);
        s->wifi_typing_name=false;s->keyboard[0]=0;s->keyboard_selected=0;s->destination_notice[0]=0;
        return KUI_SHELL_NONE;
    }
    /* A network known to be secured needs its password: 8 to 63
     * characters, or 64 hex digits. One typed by name may be open. */
    bool required=s->wifi_security && s->wifi_security!=0xffu;
    if((required || n) && (n<8 || n>KWM_PASSWORD_MAX)) {
        kui_shell_destination_error(s,"A Wi-Fi password has 8 to 63 characters.");
        return KUI_SHELL_NONE;
    }
    enum kui_shell_action action=wifi_join(s,s->keyboard);
    wifi_keyboard_close(s);
    return action;
}
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
